ernesto-g/modular-synth/FINISHED/ATVMixer/Front Panel Blueprint/ATV_MIXER_front_panel.png

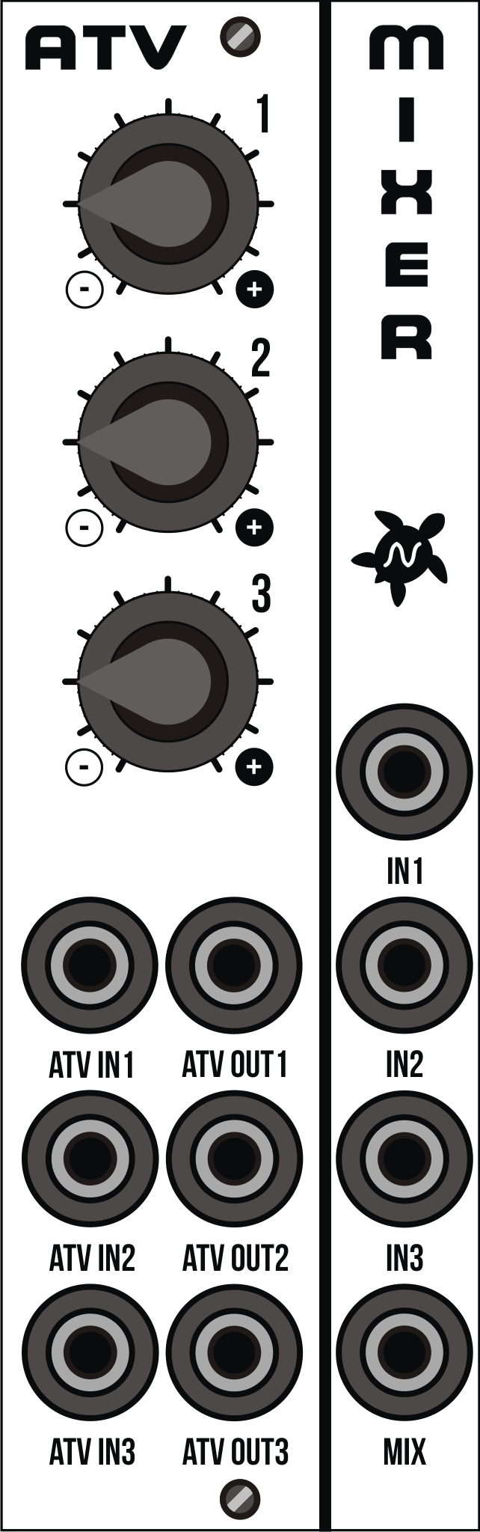
FINISHED/ATVMixer/Front Panel Blueprint/ATV_MIXER_front_panel.png
