ernesto-g/modular-synth/FINISHED/ATVMixer/PICTURES/1.jpg

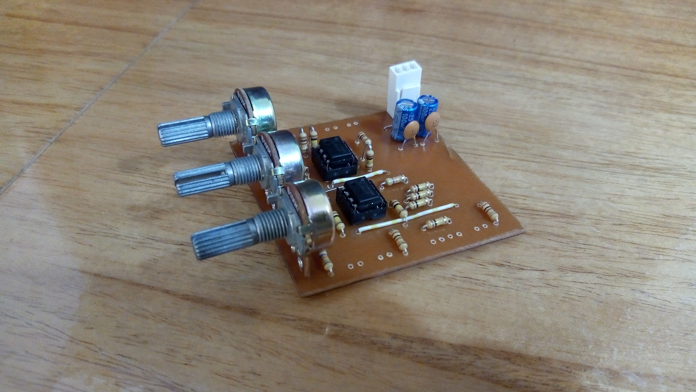
FINISHED/ATVMixer/PICTURES/1.jpg
