ernesto-g/modular-synth/FINISHED/ATVMixer/PICTURES/2.jpg

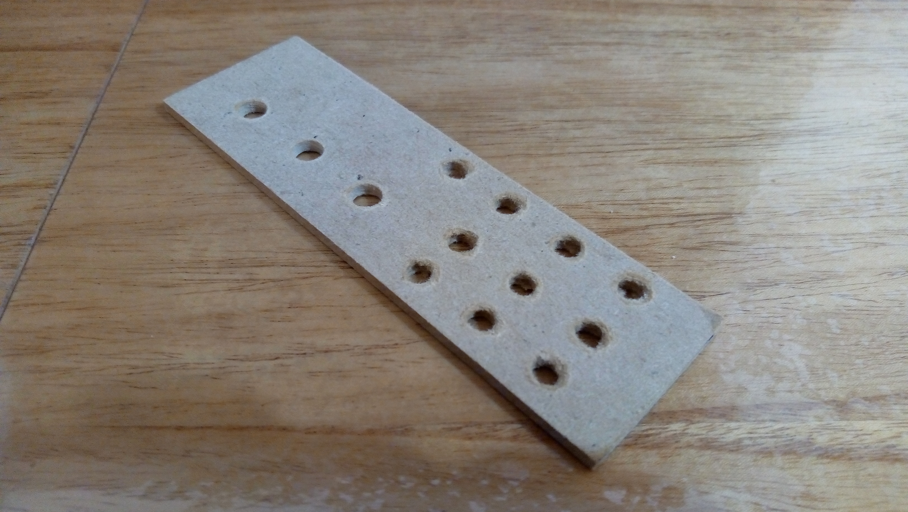
FINISHED/ATVMixer/PICTURES/2.jpg
