ernesto-g/modular-synth/FINISHED/IOS/Front Panel Blueprint/FRONT_PANEL_IOS.png

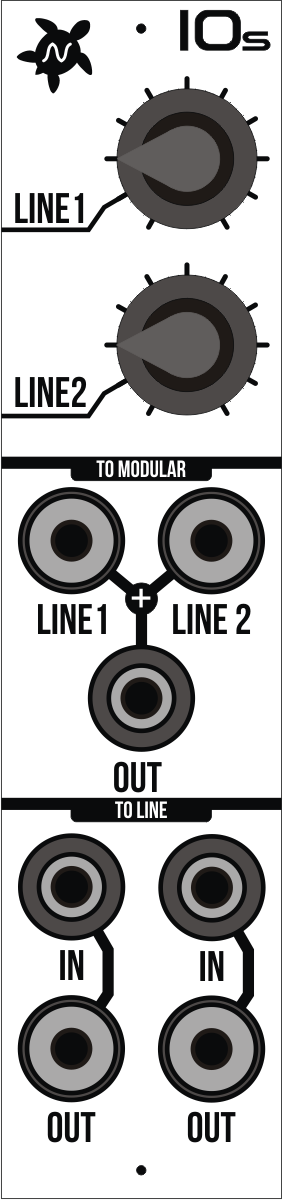
FINISHED/IOS/Front Panel Blueprint/FRONT_PANEL_IOS.png
