ernesto-g/modular-synth/FINISHED/IOS/IOSData/Line_levels.svg.png

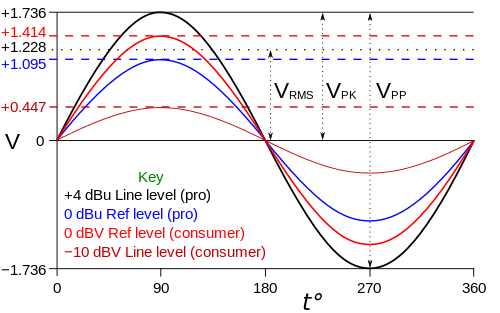
FINISHED/IOS/IOSData/Line_levels.svg.png
