ernesto-g/modular-synth/FINISHED/LFOx3/Front Panel Blueprint/LFO_X3_Front_Panel.png

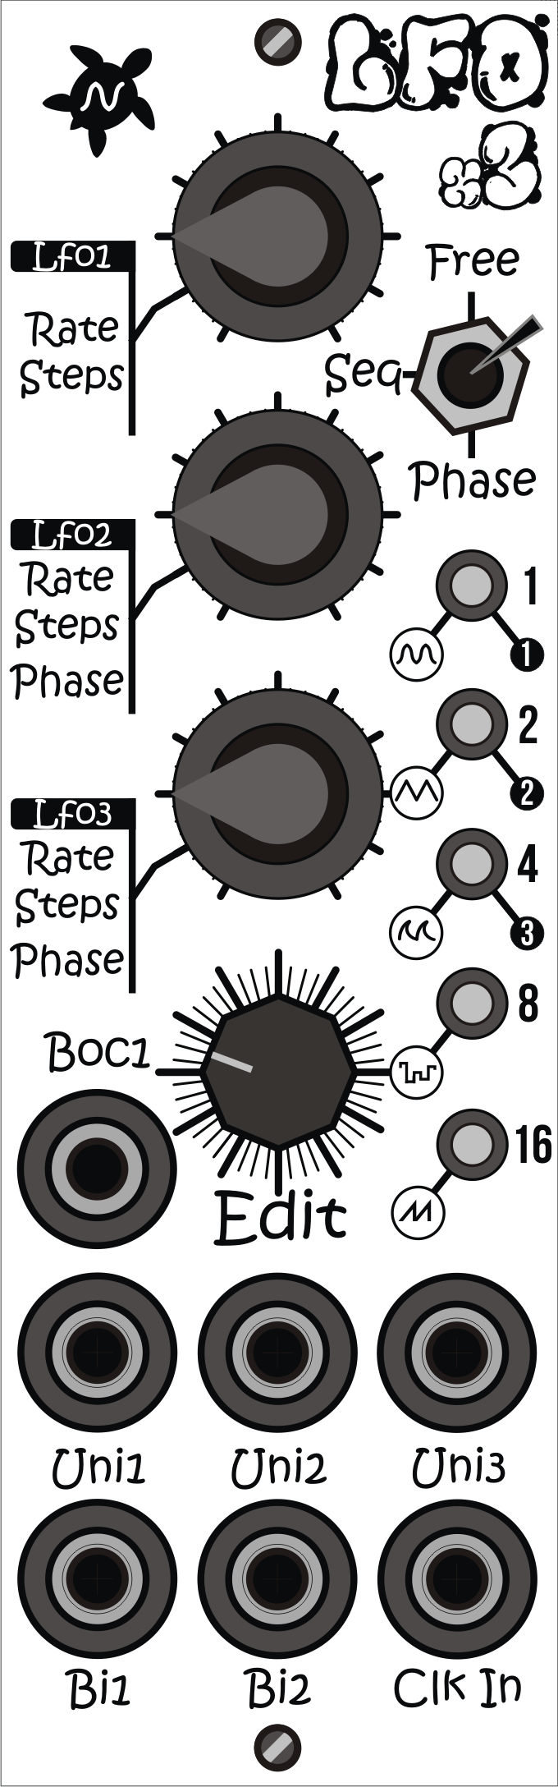
FINISHED/LFOx3/Front Panel Blueprint/LFO_X3_Front_Panel.png
