ernesto-g/modular-synth/FINISHED/SEQUENCER/Front Panel Blueprint/Font/A-Space_750.png

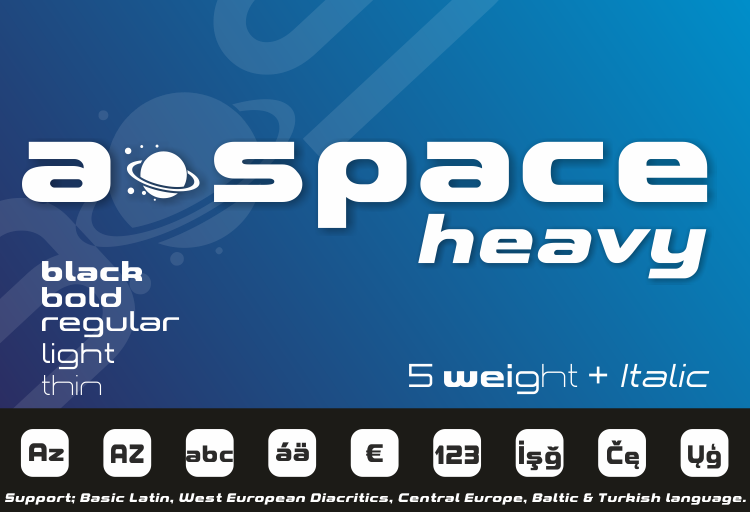
FINISHED/SEQUENCER/Front Panel Blueprint/Font/A-Space_750.png
