ernesto-g/modular-synth/FINISHED/SEQUENCER/Front Panel Blueprint/SEQ_FRONT_PANEL.png

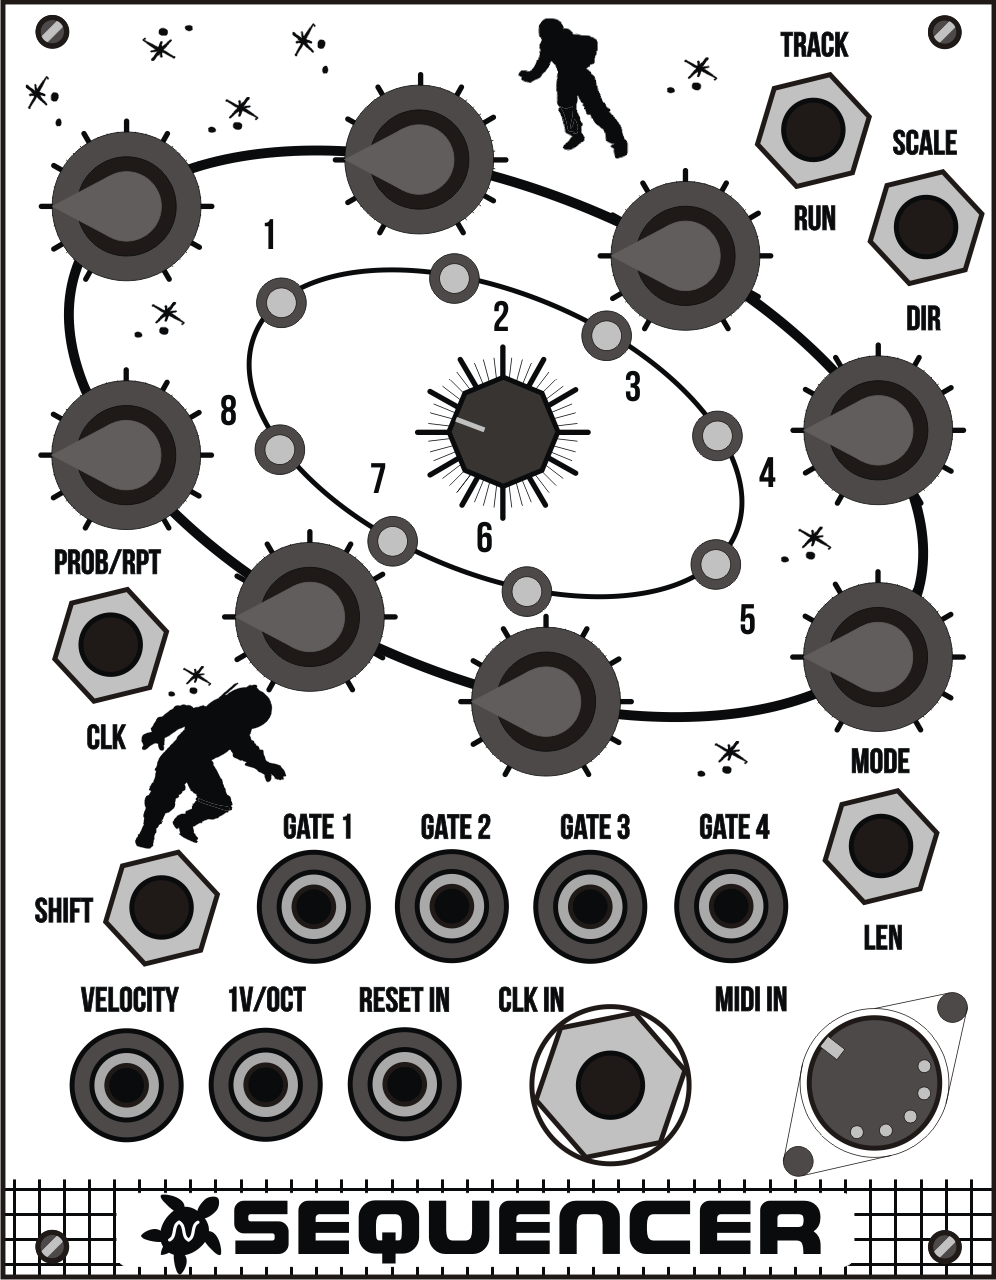
FINISHED/SEQUENCER/Front Panel Blueprint/SEQ_FRONT_PANEL.png
