ernesto-g/modular-synth/FINISHED/SIMPLE_SEQUENCER/Front Panel Blueprint/SIMPLE_SEQUENCER_Front_Panel.png

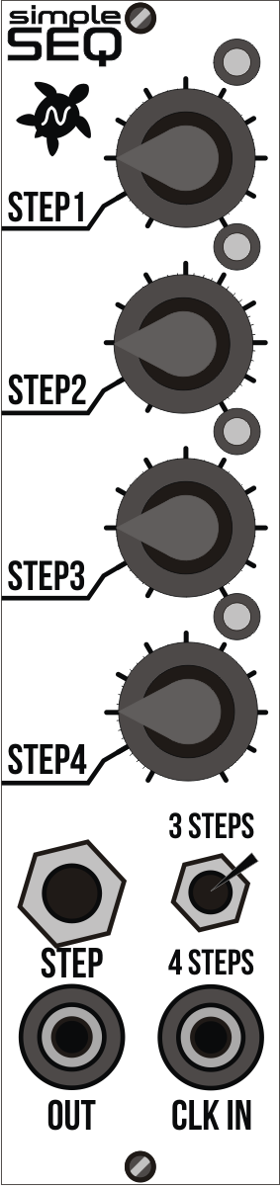
FINISHED/SIMPLE_SEQUENCER/Front Panel Blueprint/SIMPLE_SEQUENCER_Front_Panel.png
