ernesto-g/modular-synth/FINISHED/SIMPLE_SEQUENCER/PICTURES/1.jpg

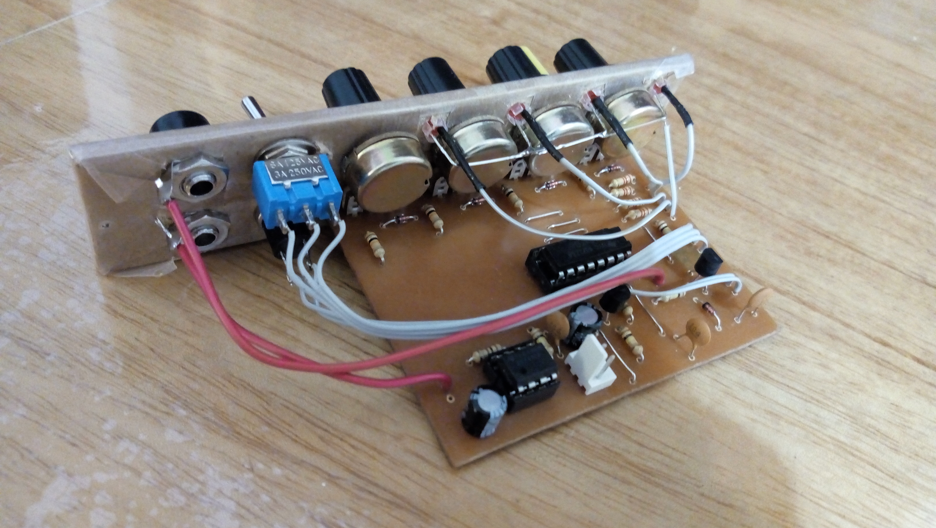
FINISHED/SIMPLE_SEQUENCER/PICTURES/1.jpg
