ernesto-g/modular-synth/FINISHED/SIMPLE_SEQUENCER/PICTURES/2.jpg

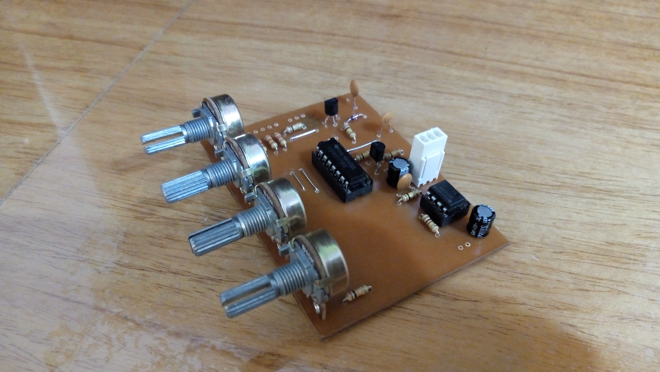
FINISHED/SIMPLE_SEQUENCER/PICTURES/2.jpg
