ernesto-g/modular-synth/FINISHED/SIMPLE_SEQUENCER/PICTURES/3.jpg

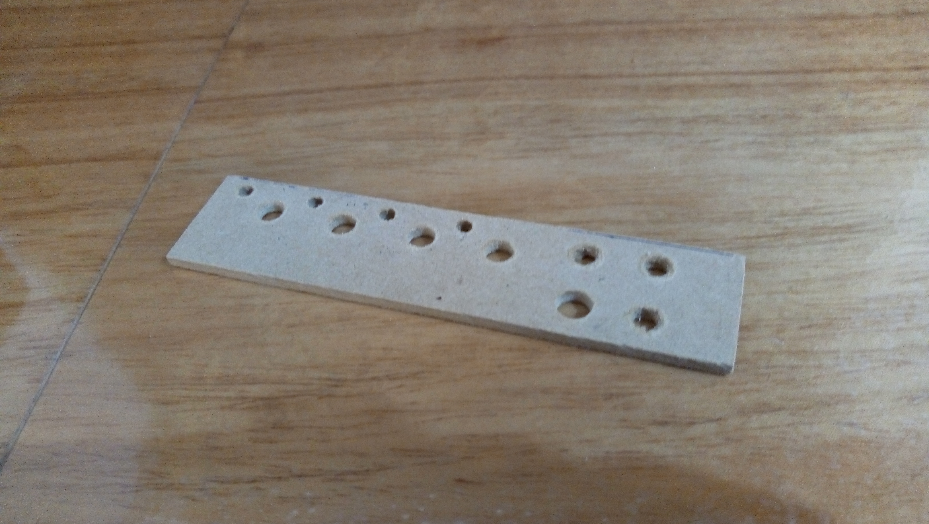
FINISHED/SIMPLE_SEQUENCER/PICTURES/3.jpg
