ernesto-g/modular-synth/FINISHED/SLEW_LIMITER/Front Panel Blueprint/FRONT_PANEL_SLEW_LIMITER.png

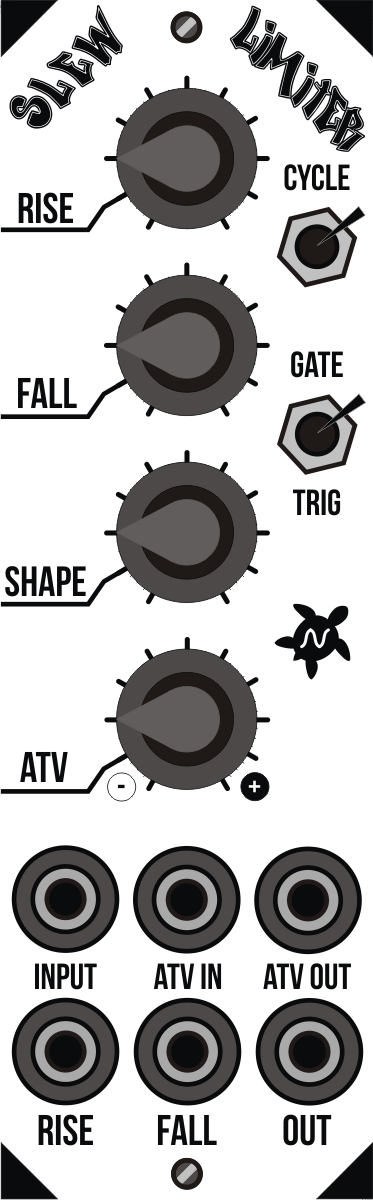
FINISHED/SLEW_LIMITER/Front Panel Blueprint/FRONT_PANEL_SLEW_LIMITER.png
