ernesto-g/modular-synth/FINISHED/SOUND_SOURCE/Front_Panel_blueprint/SOUND_SOURCE_FRONT_PANEL.png

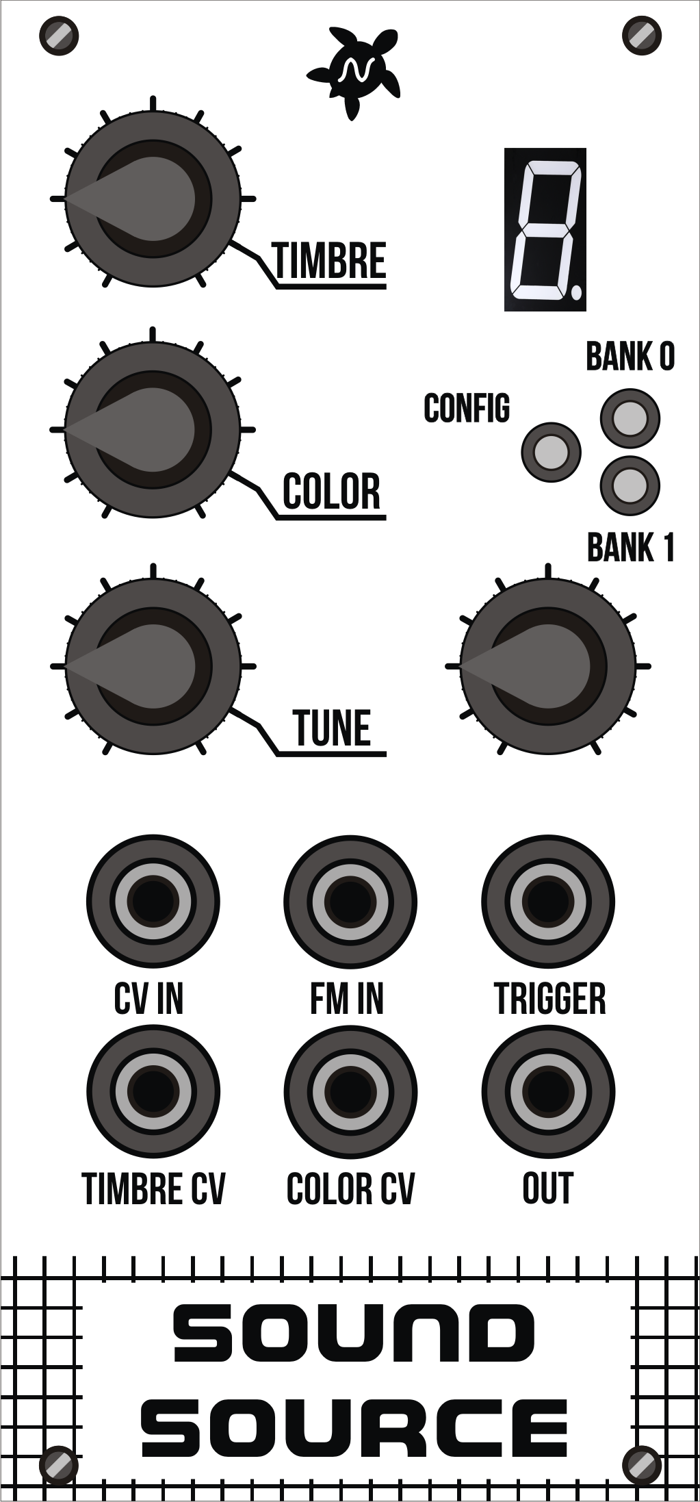
FINISHED/SOUND_SOURCE/Front_Panel_blueprint/SOUND_SOURCE_FRONT_PANEL.png
