ernesto-g/modular-synth/FINISHED/SOUND_SOURCE/Pictures/1.png

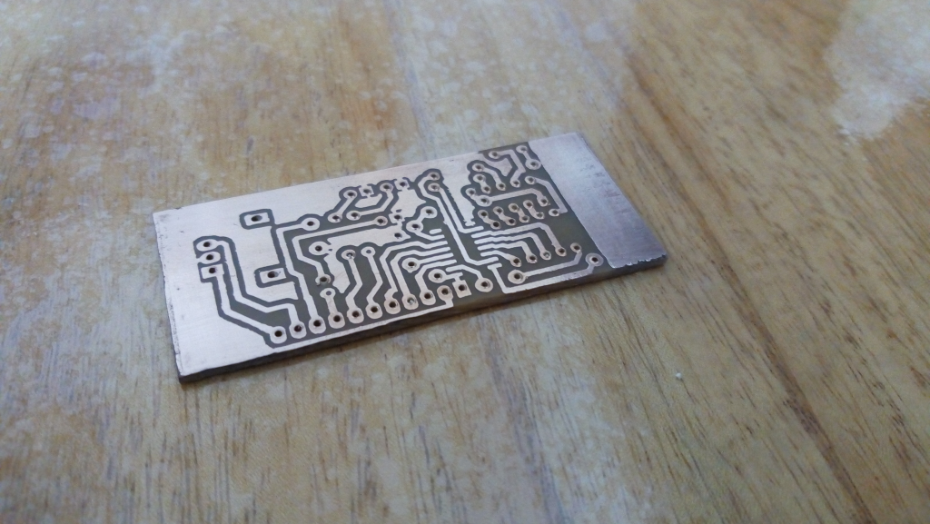
FINISHED/SOUND_SOURCE/Pictures/1.png
