ernesto-g/modular-synth/FINISHED/SOUND_SOURCE/Pictures/2.png

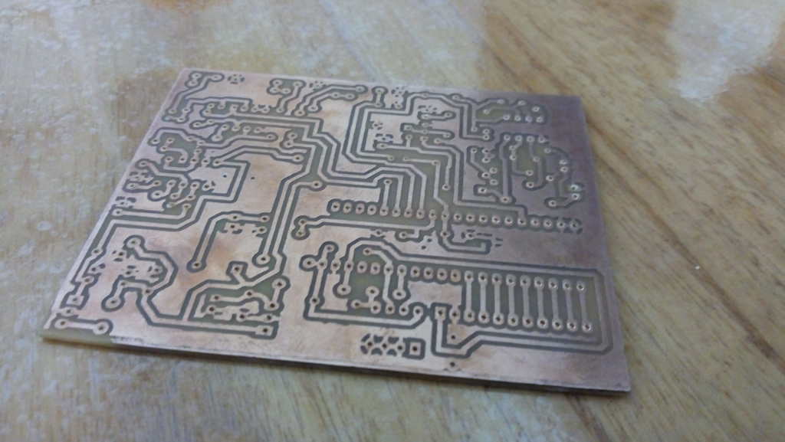
FINISHED/SOUND_SOURCE/Pictures/2.png
