ernesto-g/modular-synth/FINISHED/SOUND_SOURCE/Pictures/3.png

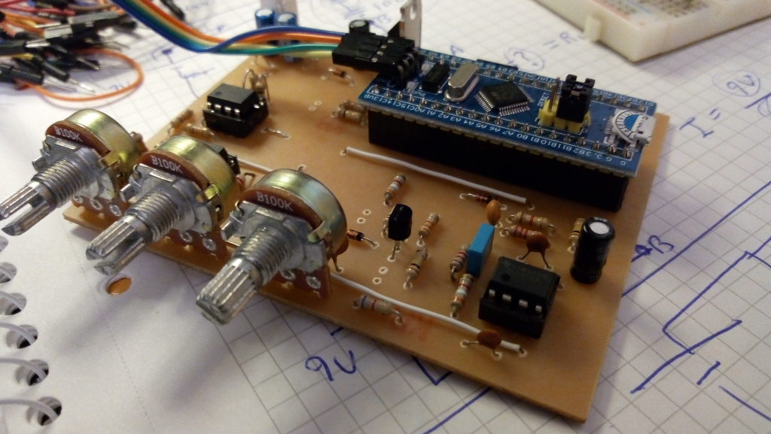
FINISHED/SOUND_SOURCE/Pictures/3.png
