ernesto-g/modular-synth/FINISHED/SOUND_SOURCE/Pictures/4.png

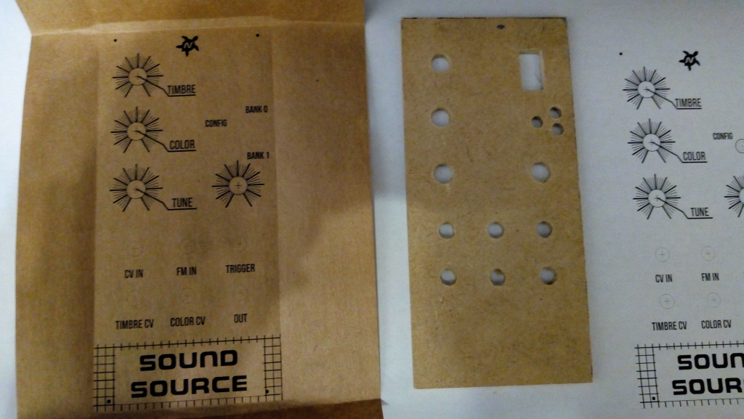
FINISHED/SOUND_SOURCE/Pictures/4.png
