ernesto-g/modular-synth/FINISHED/SOUND_SOURCE/Pictures/6.png

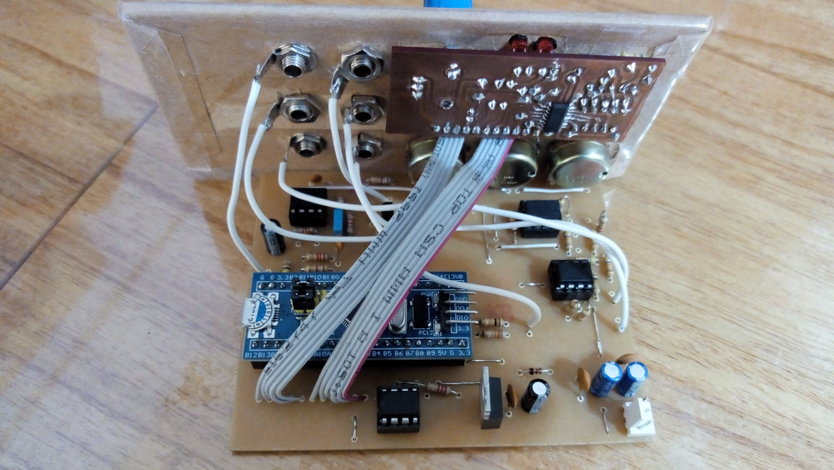
FINISHED/SOUND_SOURCE/Pictures/6.png
