ernesto-g/modular-synth/FINISHED/SOUND_SOURCE/Pictures/7.png

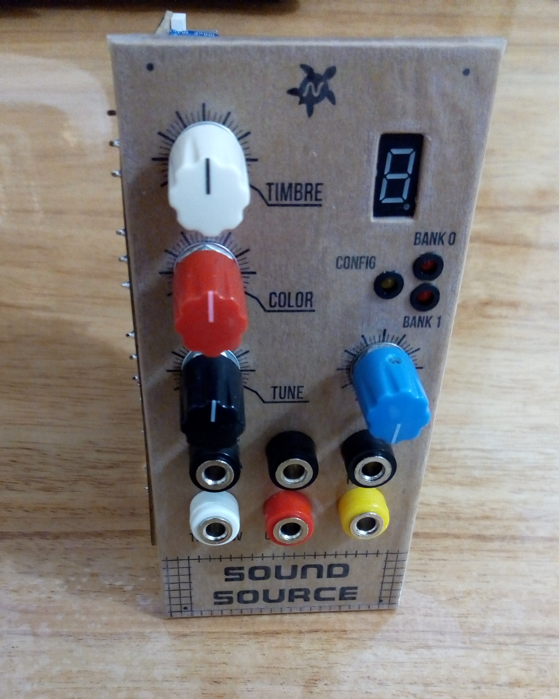
FINISHED/SOUND_SOURCE/Pictures/7.png
