ernesto-g/modular-synth/FINISHED/SOUND_SOURCE/Pictures/8.png

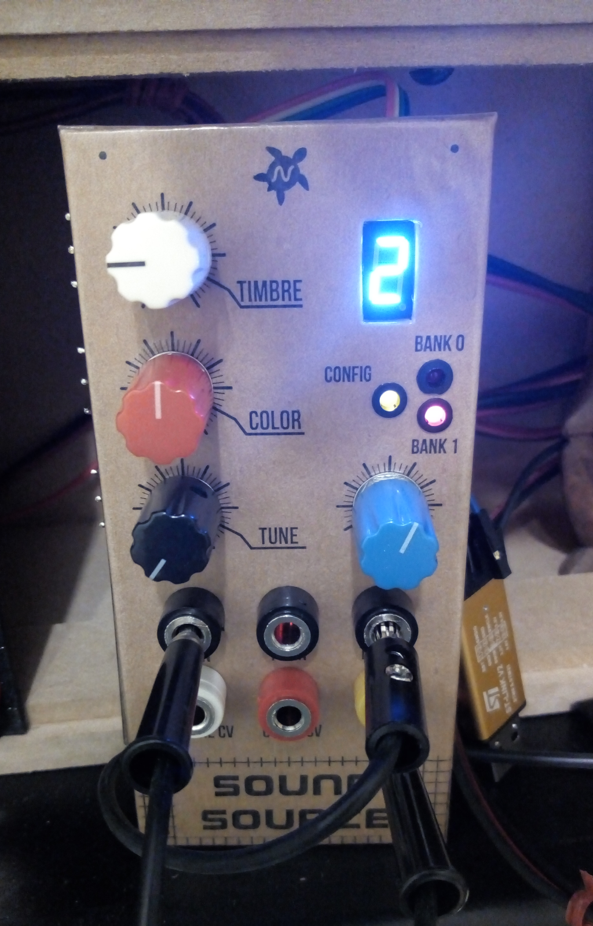
FINISHED/SOUND_SOURCE/Pictures/8.png
