ernesto-g/modular-synth/FINISHED/VCA/Front Panel Blueprint/VCA_FRONT_PANEL.png

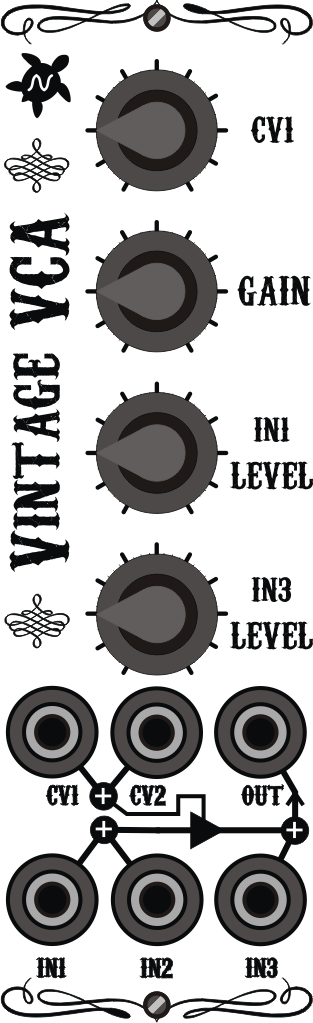
FINISHED/VCA/Front Panel Blueprint/VCA_FRONT_PANEL.png
