ernesto-g/modular-synth/FINISHED/VCO/Front panel blueprint/VCO_FRONT_PANEL.png

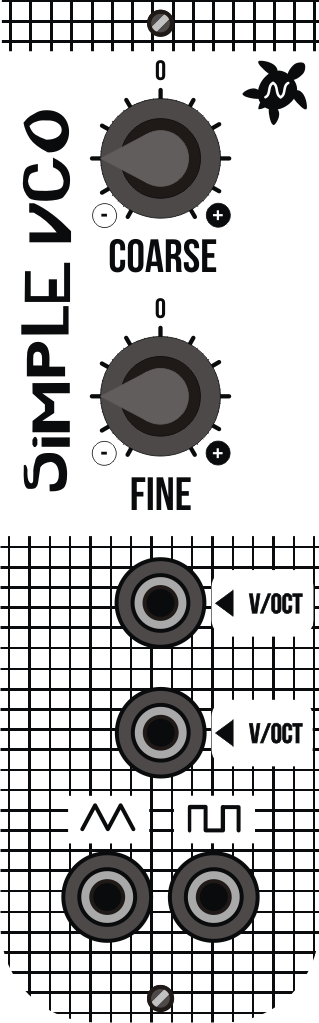
FINISHED/VCO/Front panel blueprint/VCO_FRONT_PANEL.png
