ernesto-g/modular-synth/UNFINISHED/INDUSTRIAL_KICK/signal_1.png

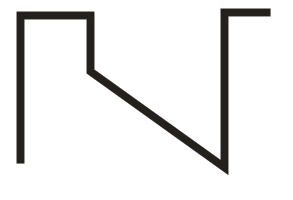
UNFINISHED/INDUSTRIAL_KICK/signal_1.png
