ernesto-g/modular-synth/UNFINISHED/INDUSTRIAL_KICK/signal_2.png

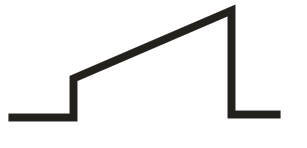
UNFINISHED/INDUSTRIAL_KICK/signal_2.png
