ernesto-g/modular-synth/UNFINISHED/INDUSTRIAL_KICK/signal_3.png

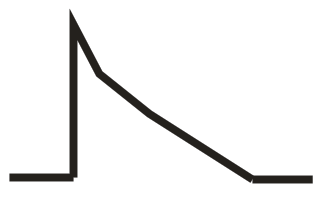
UNFINISHED/INDUSTRIAL_KICK/signal_3.png
