ernesto-g/modular-synth/UNFINISHED/INDUSTRIAL_KICK/signal_4.png

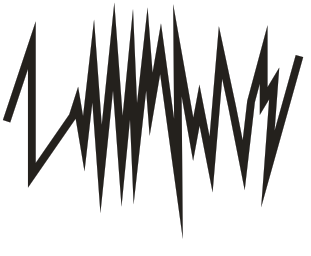
UNFINISHED/INDUSTRIAL_KICK/signal_4.png
