ernesto-g/modular-synth/FINISHED/SIMPLE_SEQUENCER/SIMPLE_SEQUENCER_modular_PCB/DIY/SIMPLE_SEQUENCER_wires_and_connectors.pdf

# Rear View

J2_1

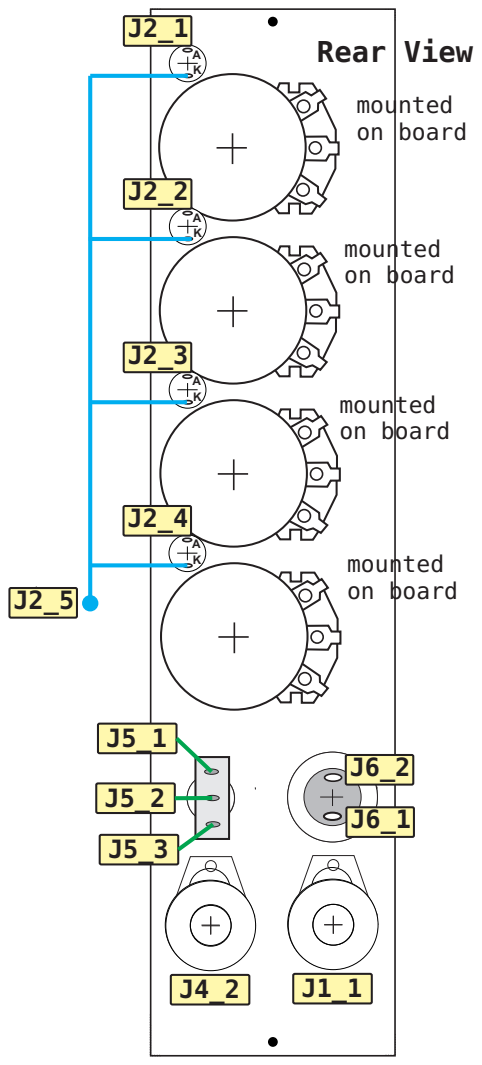
[picture p37: page 1]
mounted; on board
