ernesto-g/modular-synth/FINISHED/ATVMixer/ATV_AND_MIXER_modular_PCB/DIY/ATV_MIXER_FRONT_PANEL_HOLES.pdf

7mm

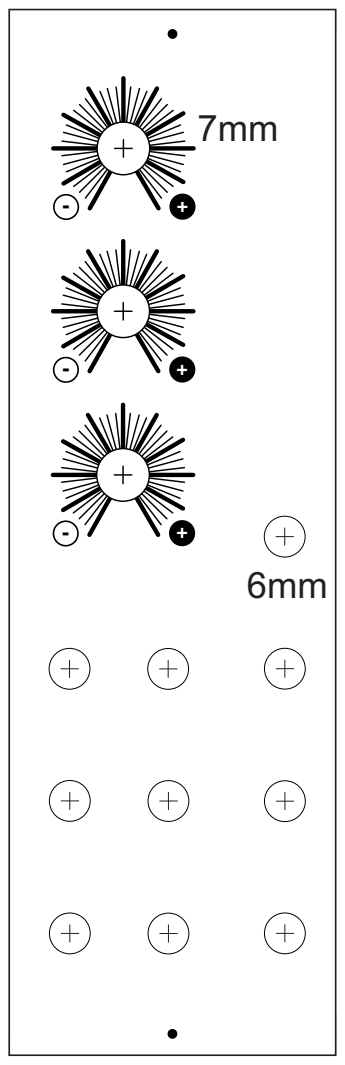
[picture p38: page 1]
