ernesto-g/modular-synth/FINISHED/ATVMixer/ATV_AND_MIXER_modular_PCB/DIY/ATV_MIXER_FRONT_PANEL_wires_and_connectors.pdf

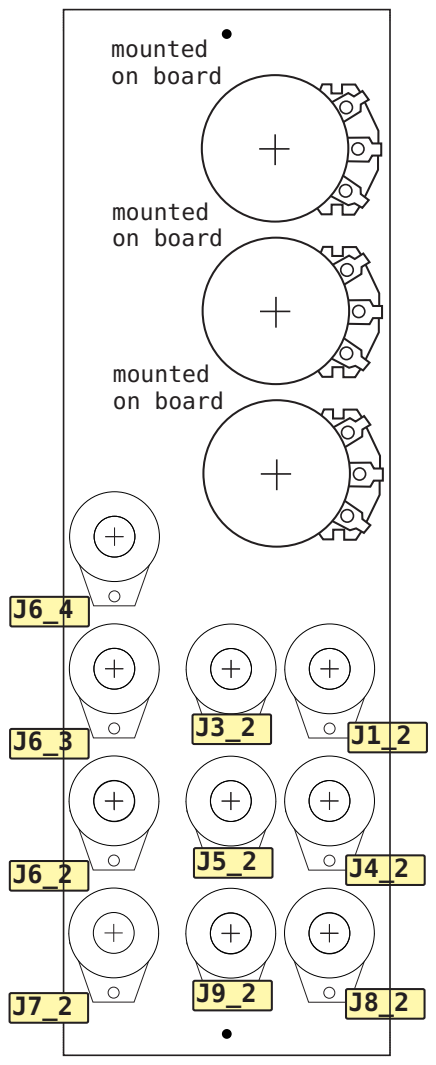
[picture p39: page 1]
mounted; on board
