ernesto-g/modular-synth/FINISHED/LFOx3/LFO_modular_PCB/DIY/LFO_X3_FRONT_PANEL_wires_and_connectors.pdf

J7_1

J7_2

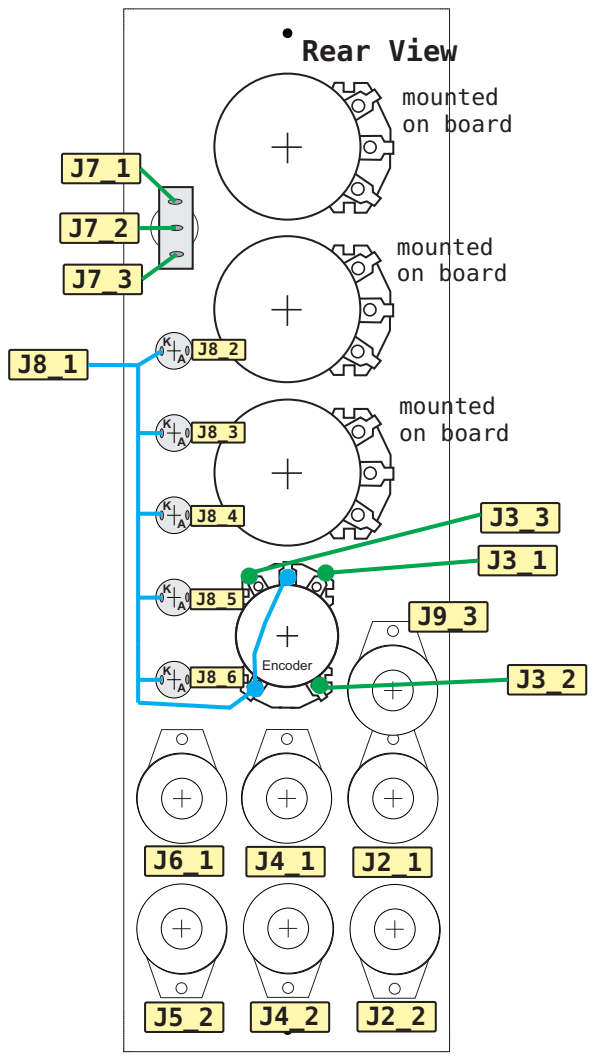
[picture p40: page 1]
mounted; on board; Rear View; Encoder
