ernesto-g/modular-synth/FINISHED/SOUND_SOURCE/SOUND_SOURCE_modular_PCB/DIY/SOUND_SOURCE_FRONT_PANEL_wires_and_connectors.pdf

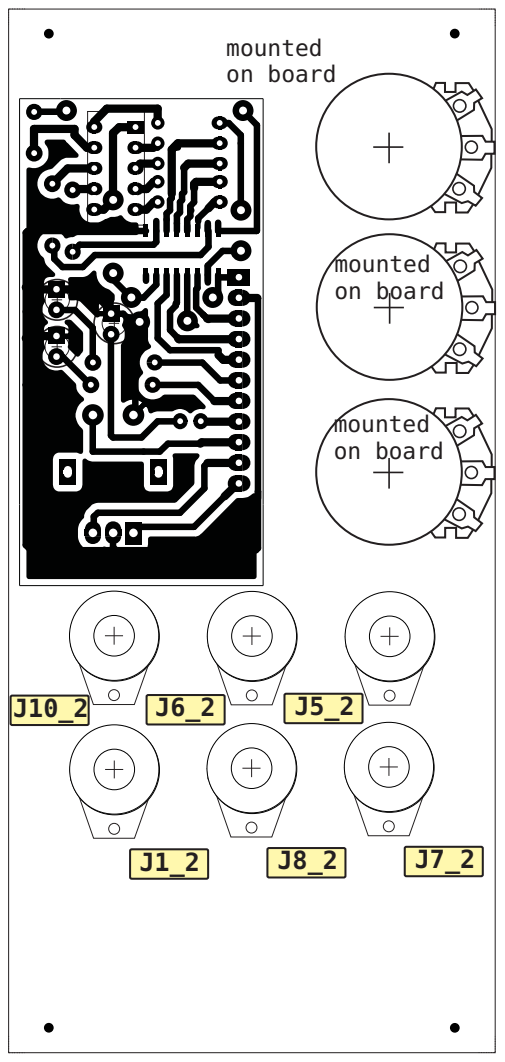
[picture p41: page 1]
mounted; on board
