ernesto-g/modular-synth/FINISHED/IOS/IOS_modular_PCB/DIY/IOS_FRONT_PANEL_wires_and_connectors.pdf

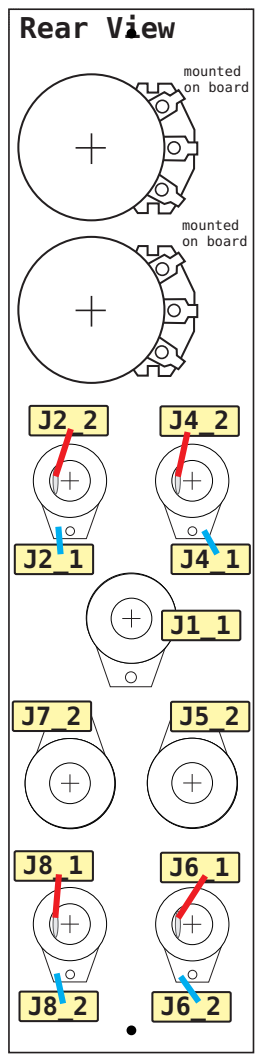
[picture p42: page 1]
mounted; on board; Rear View
