ernesto-g/modular-synth/FINISHED/SEQUENCER/SEQUENCER_modular_PCB/DIY/SEQ_FRONT_PANEL.pdf

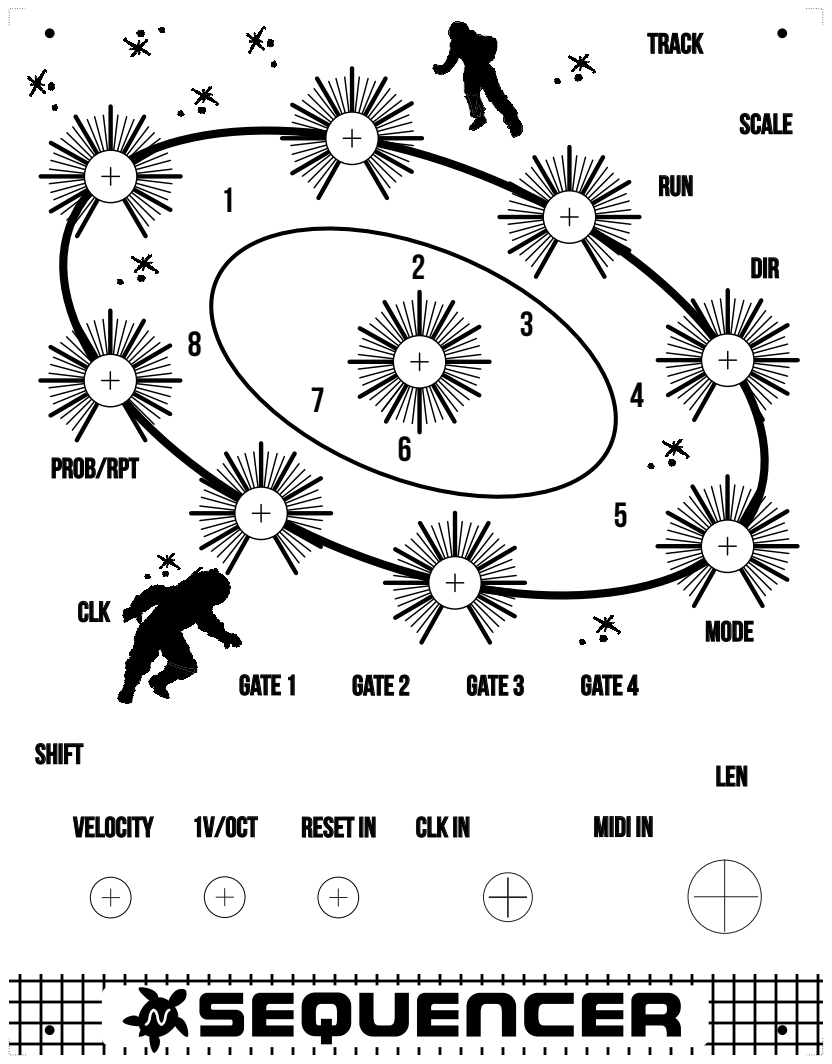
[picture p43: page 1]
VELOCITY; 1V/oct; RESET IN; CLK IN; TRACK; RUN; MODE; LEN; CLK; PROB/RPT; SHIFT; SCALE; DIR; MIDI IN; Gate 1; Gate 2; Gate 3; Gate 4; SEQUENCER
