ernesto-g/modular-synth/FINISHED/SEQUENCER/SEQUENCER_modular_PCB/DIY/SEQ_FRONT_PANEL_wires_and_connectors.pdf

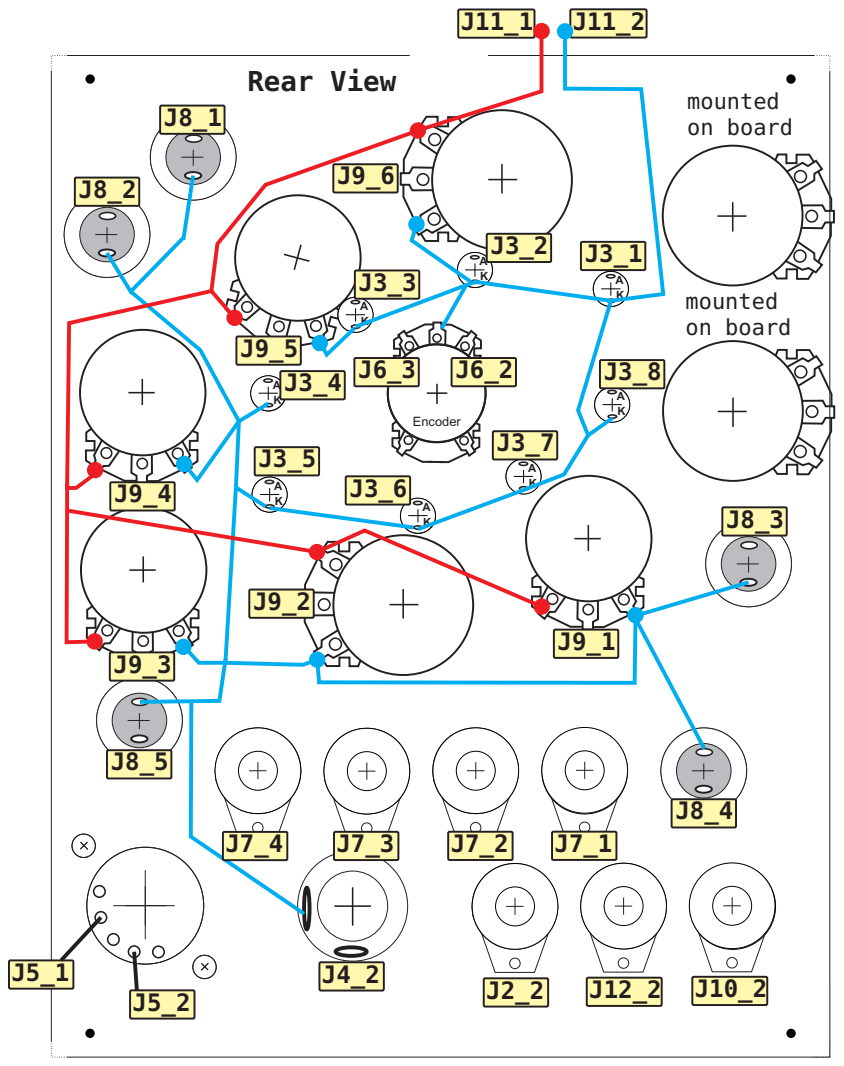
[picture p44: page 1]
Rear View; mounted; on board; Encoder
