ernesto-g/modular-synth/FINISHED/SLEW_LIMITER/SLEW_LIMITER_modular_PCB/DIY/SLEW_LIMITER_FRONT_PANEL_wires_and_connectors.pdf

# Rear View

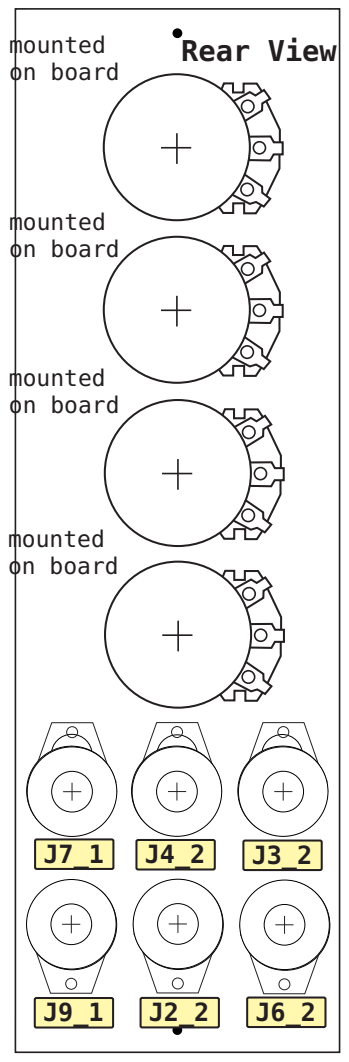
[picture p45: page 1]
mounted; on board
