ernesto-g/modular-synth/FINISHED/VCA/VCA_modular_PCB/DIY/VCA_FRONT_PANEL_wires_and_connectors.pdf

# Rear View

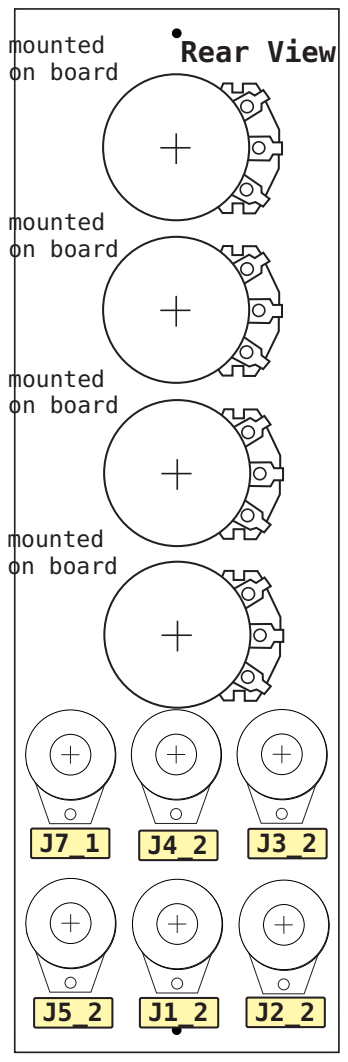
[picture p46: page 1]
mounted; on board
