ernesto-g/modular-synth/FINISHED/VCO/VCO_Modular_PCB/DIY/VCO_FRONT_PANEL_wires_and_connectors.pdf

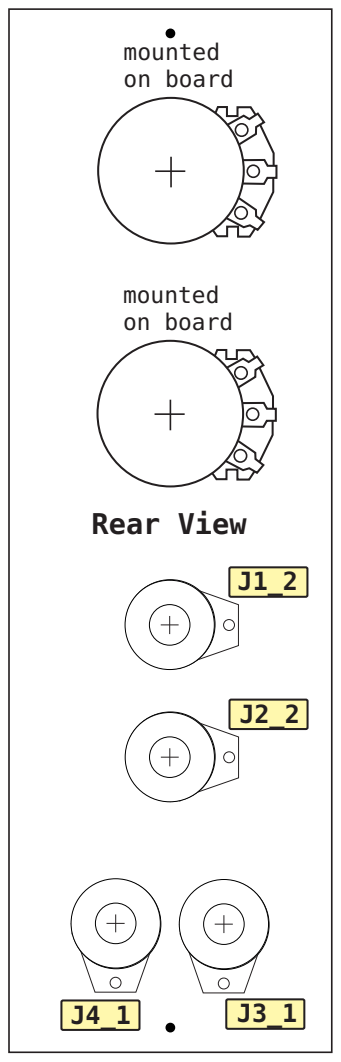
[picture p47: page 1]
Rear View; mounted; on board
