ernesto-g/modular-synth/FINISHED/SOUND_SOURCE/SOUND_SOURCE_modular_PCB/DIY/PCB_components.pdf

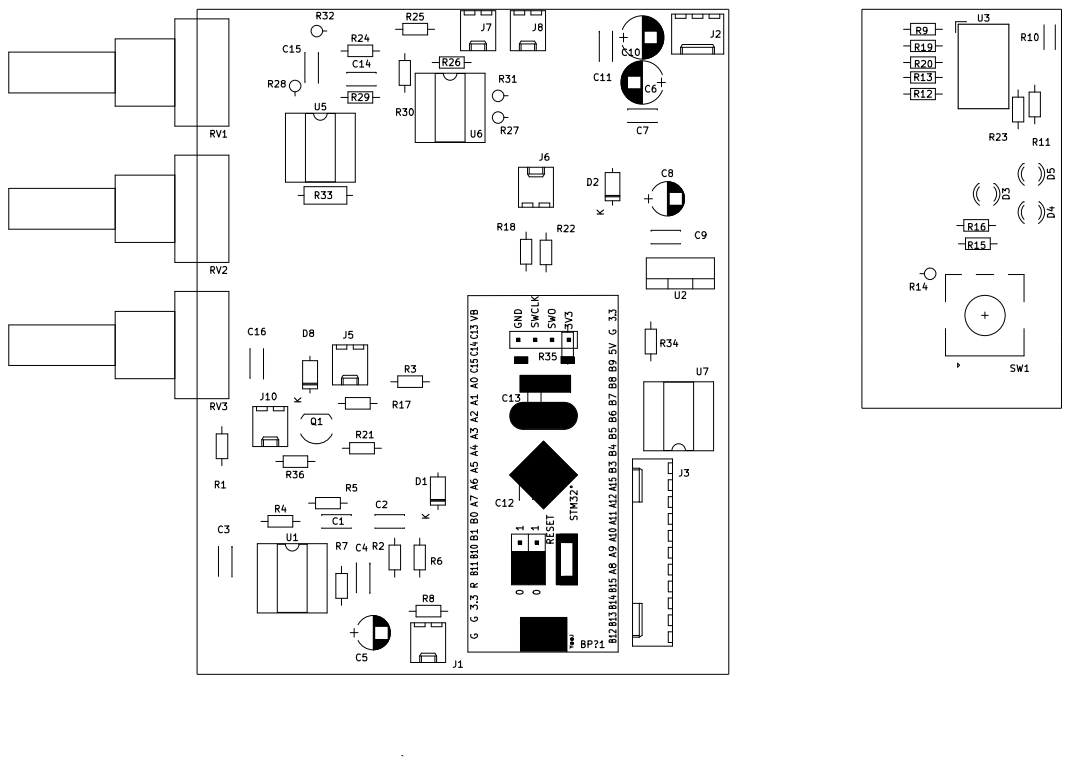
[picture p57: page 1]
