ernesto-g/modular-synth/FINISHED/IOS/IOS_modular_PCB/DIY/PCB_components.pdf

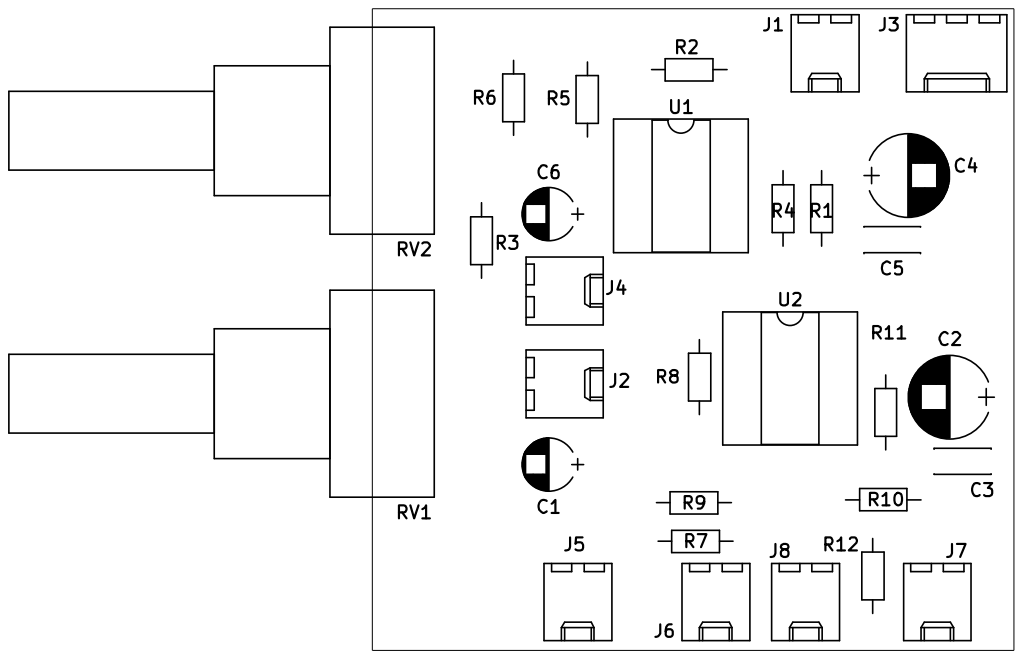
[picture p58: page 1]
