ernesto-g/modular-synth/FINISHED/IOS/IOS_modular_PCB/DIY/Schematic.pdf

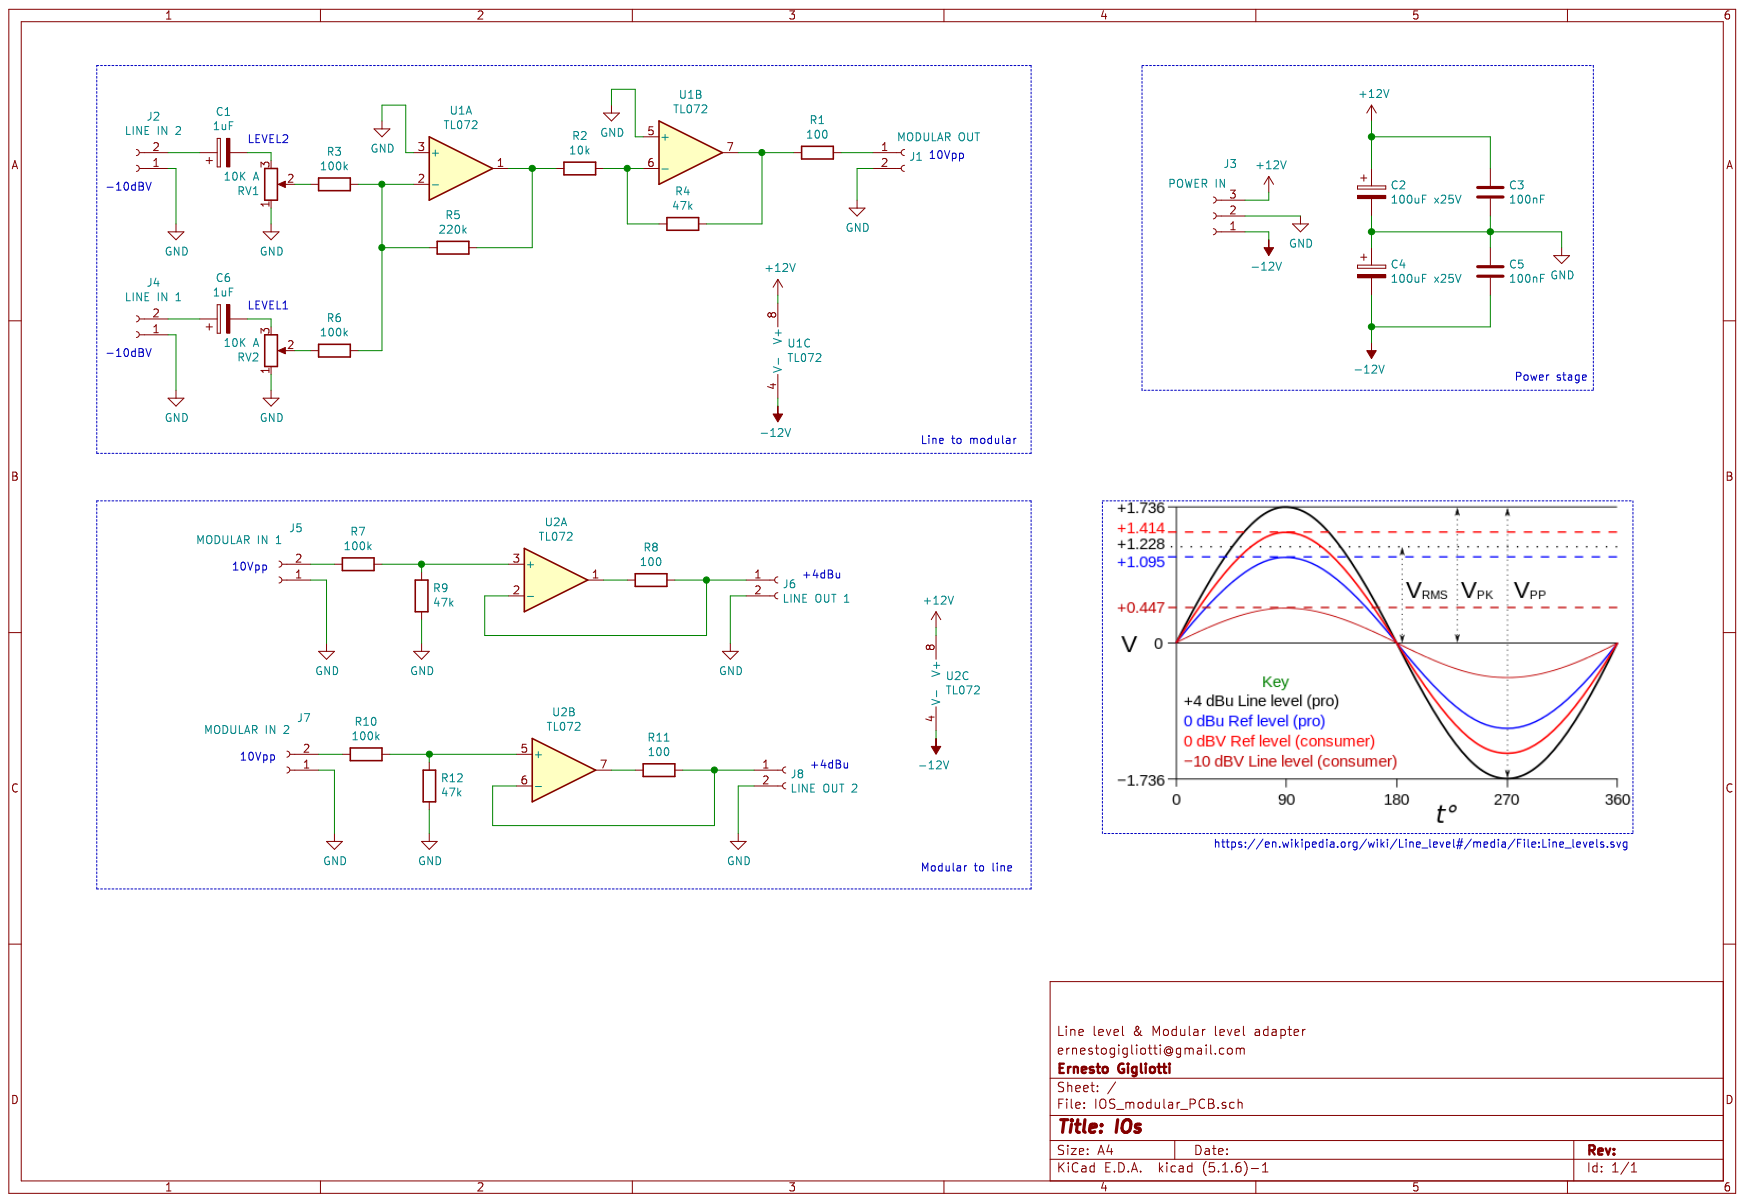
[picture p59: page 1]
