ernesto-g/modular-synth/FINISHED/SEQUENCER/SEQUENCER_modular_PCB/DIY/PCB_components.pdf

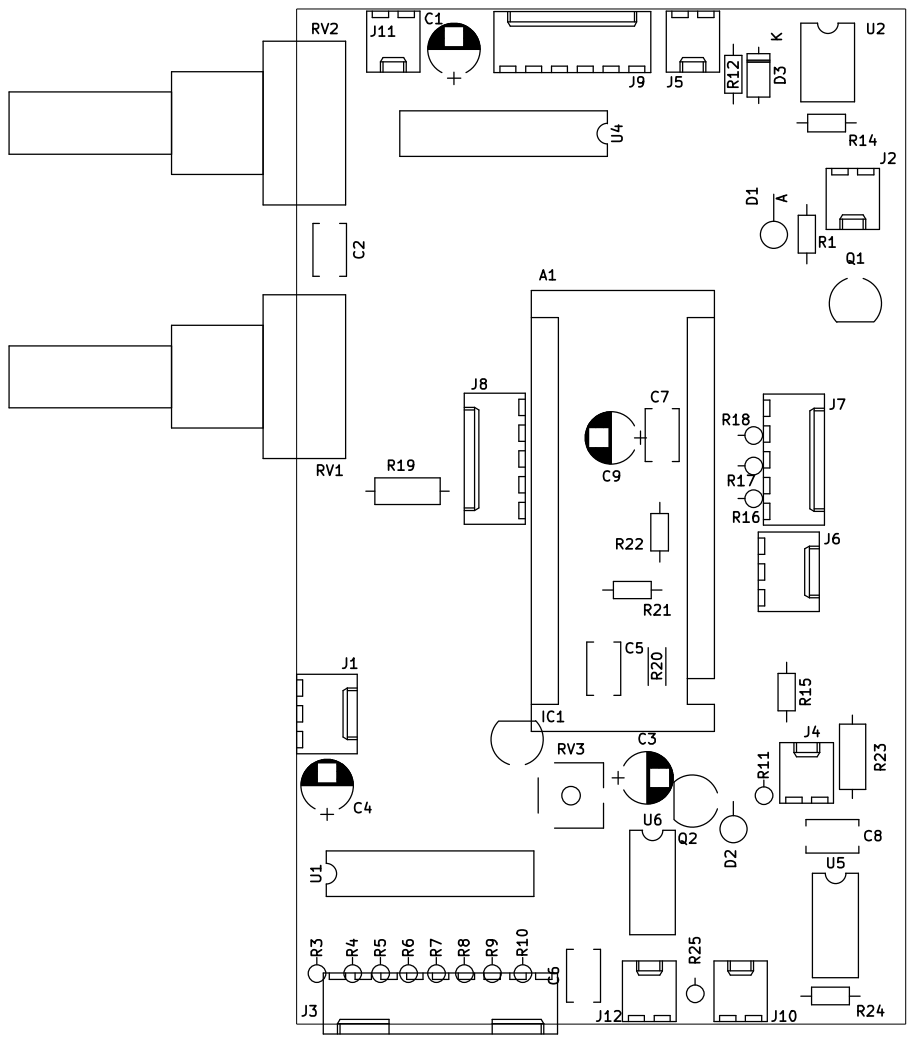
[picture p60: page 1]
