ernesto-g/modular-synth/FINISHED/SEQUENCER/SEQUENCER_modular_PCB/DIY/Schematic.pdf

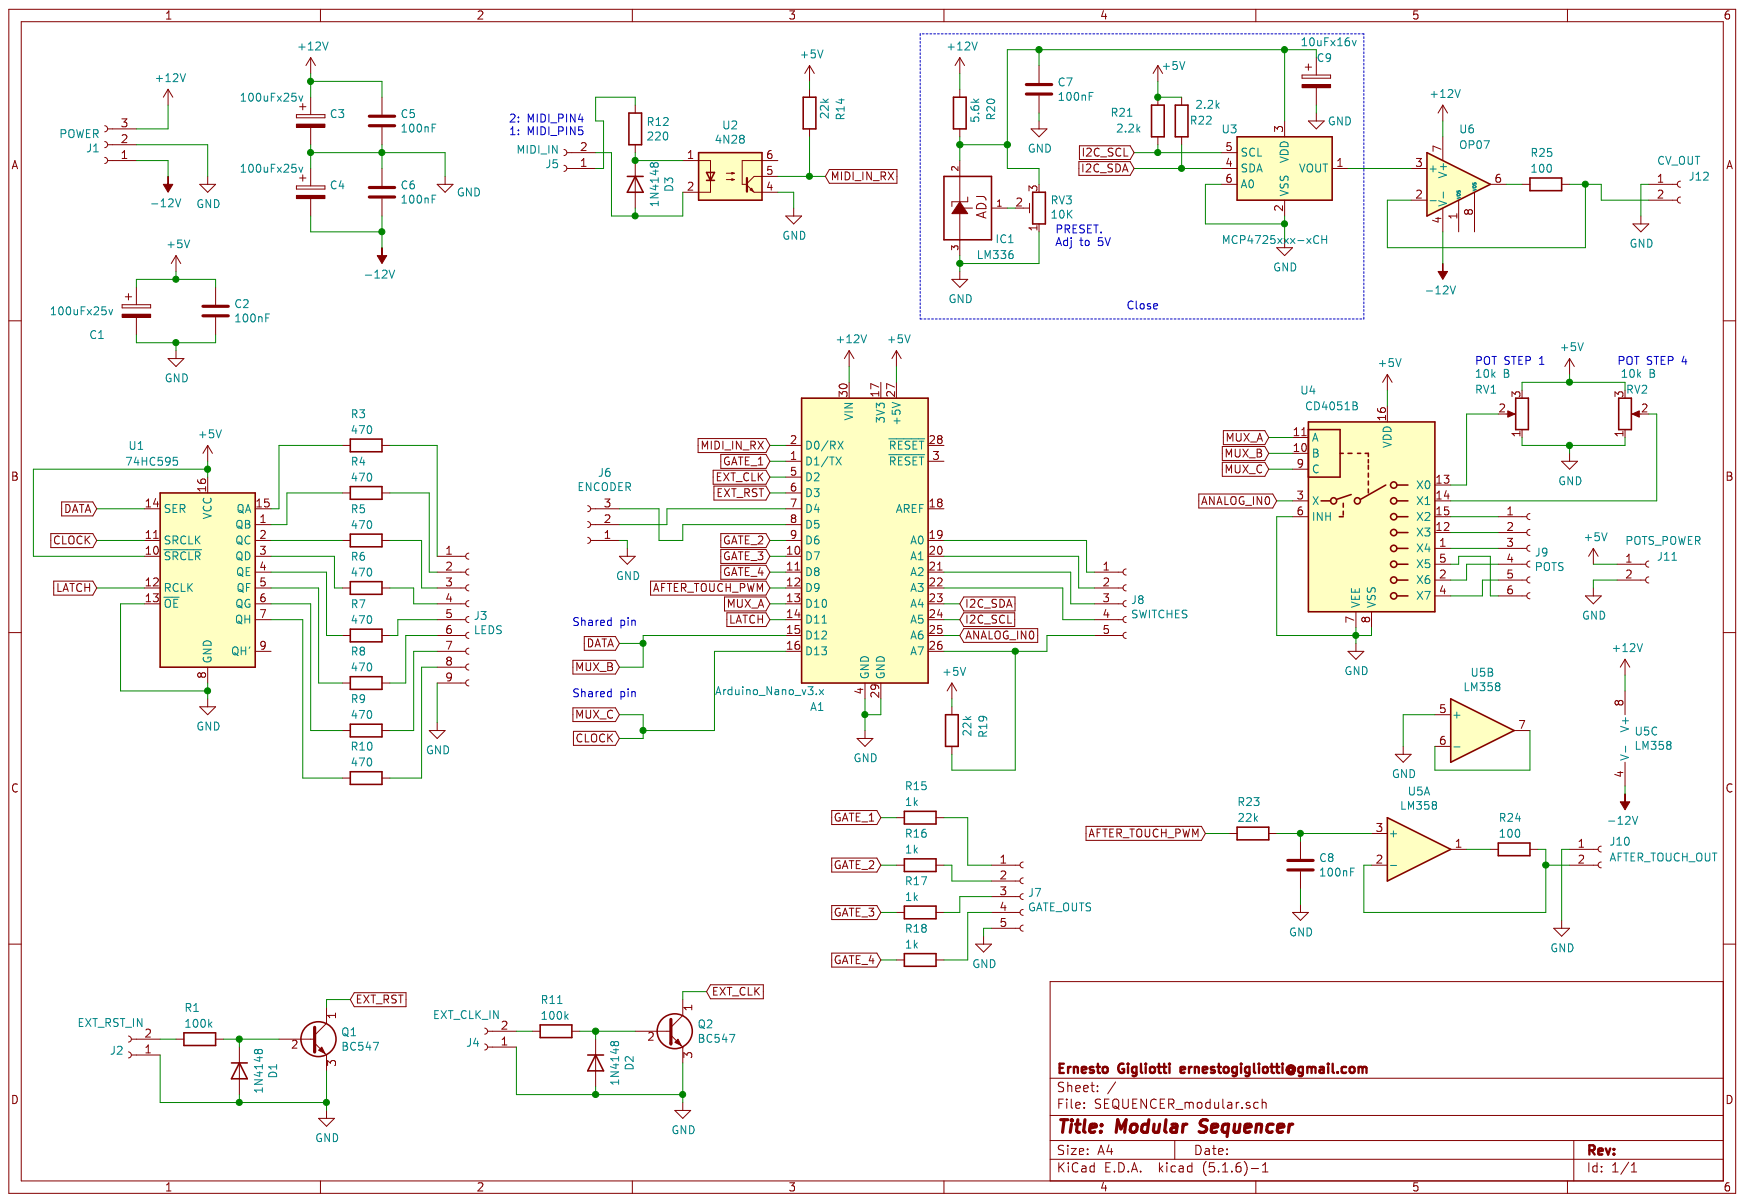
[picture p61: page 1]
