ernesto-g/modular-synth/FINISHED/SLEW_LIMITER/SLEW_LIMITER_modular_PCB/DIY/PCB_components.pdf

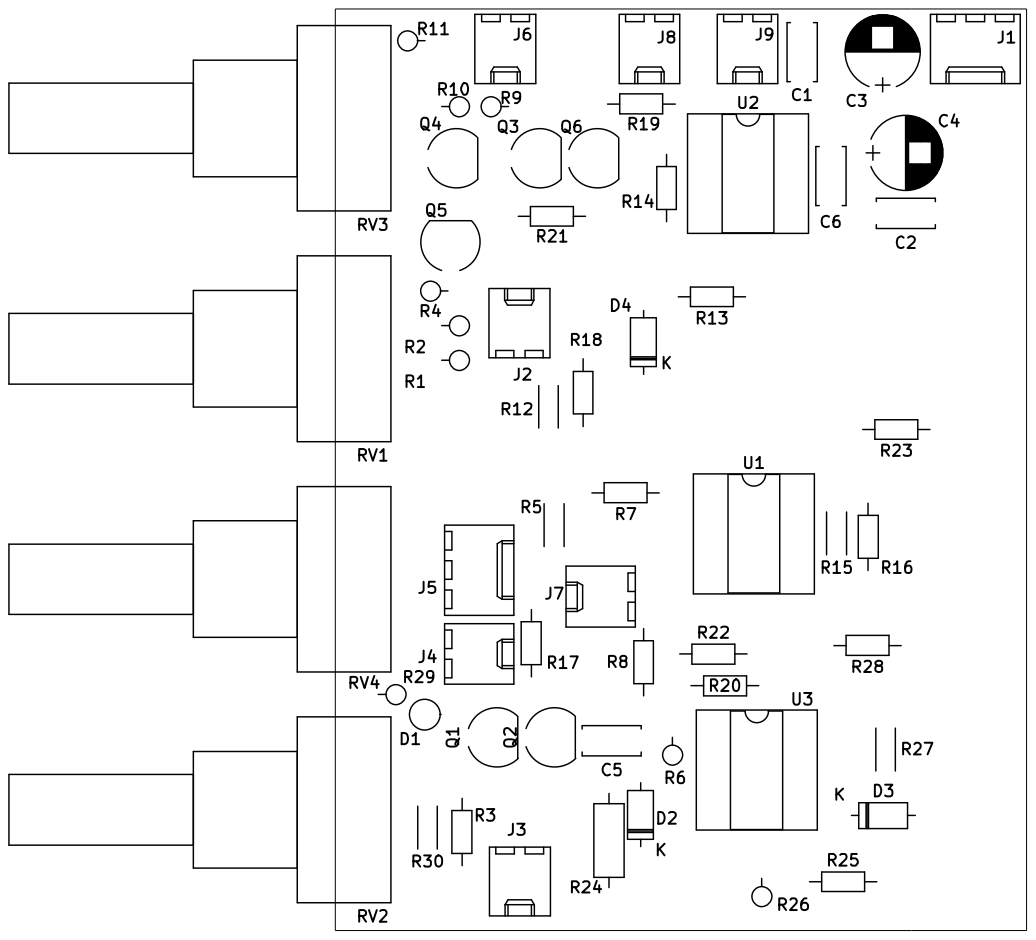
[picture p62: page 1]
