ernesto-g/modular-synth/FINISHED/SLEW_LIMITER/SLEW_LIMITER_modular_PCB/DIY/Schematic.pdf

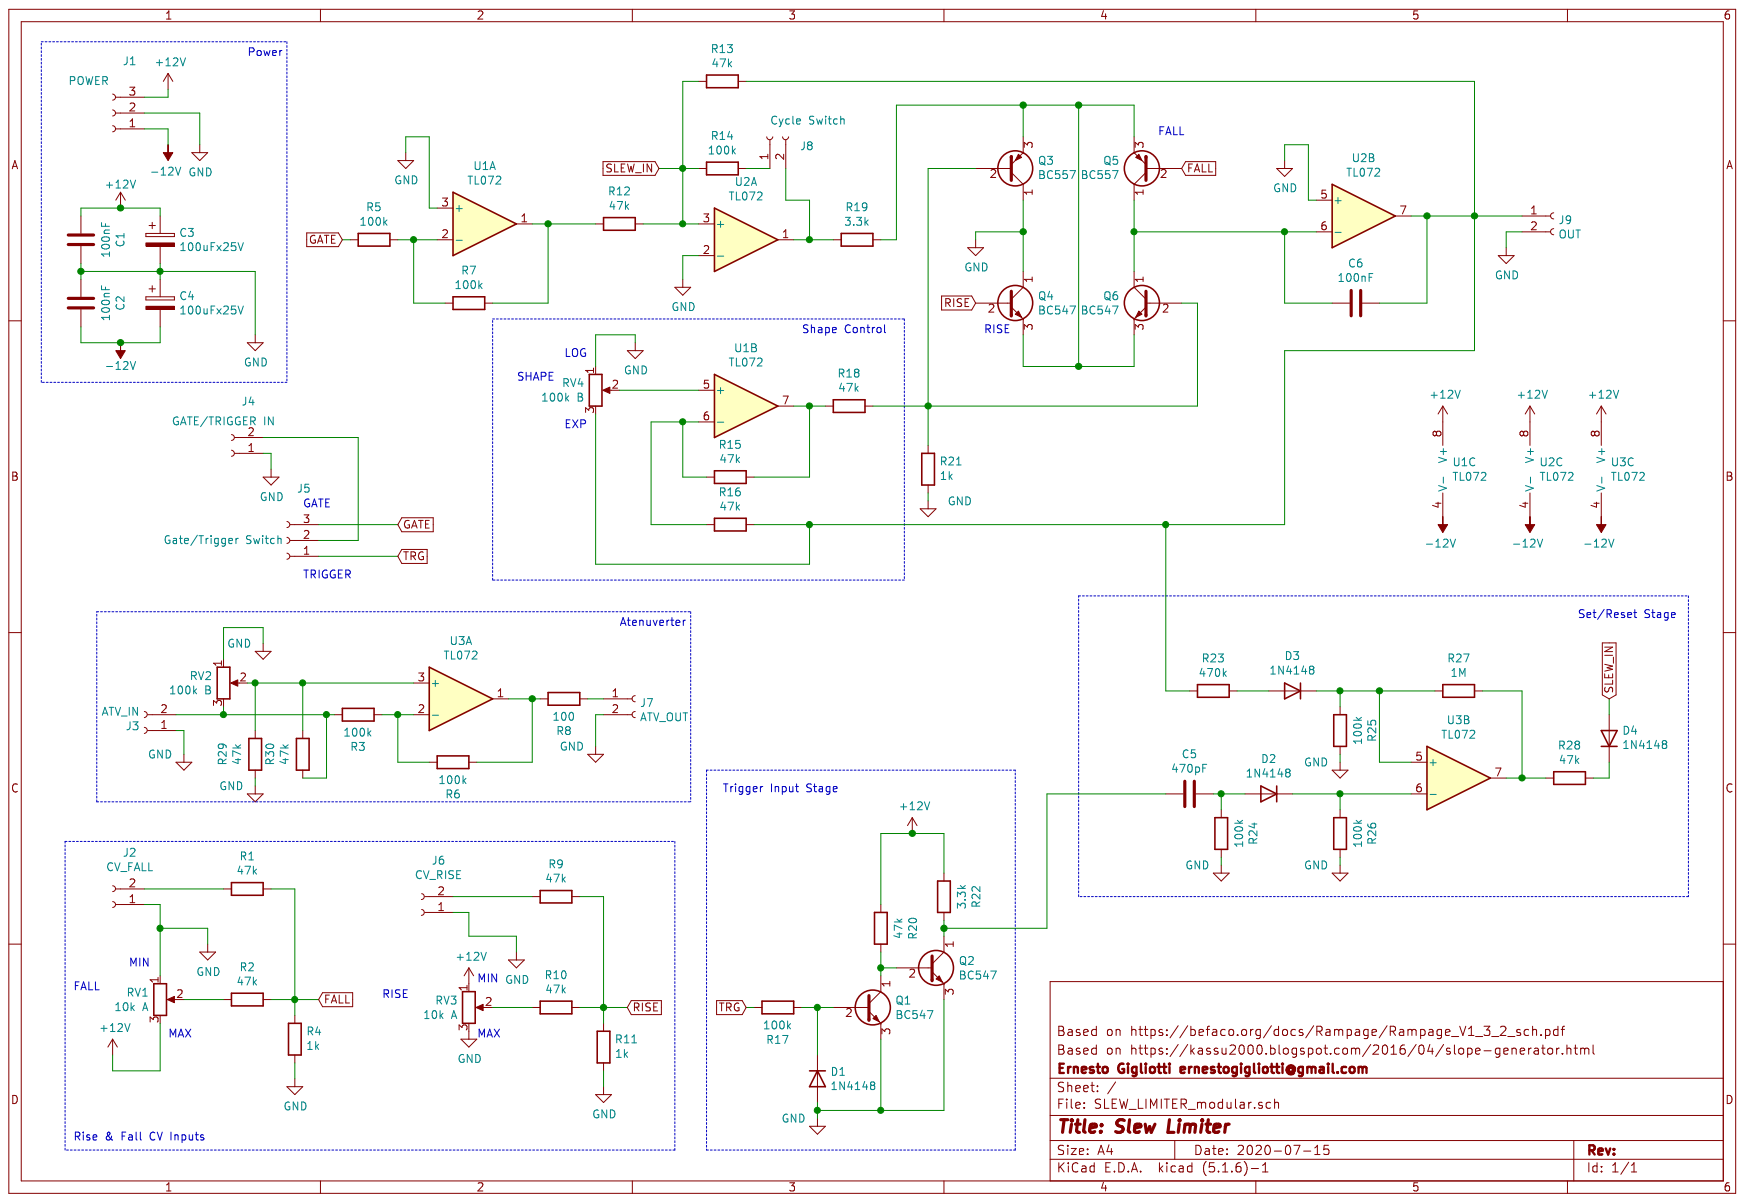
[picture p63: page 1]
