ernesto-g/modular-synth/FINISHED/VCA/VCA_modular_PCB/DIY/PCB_components.pdf

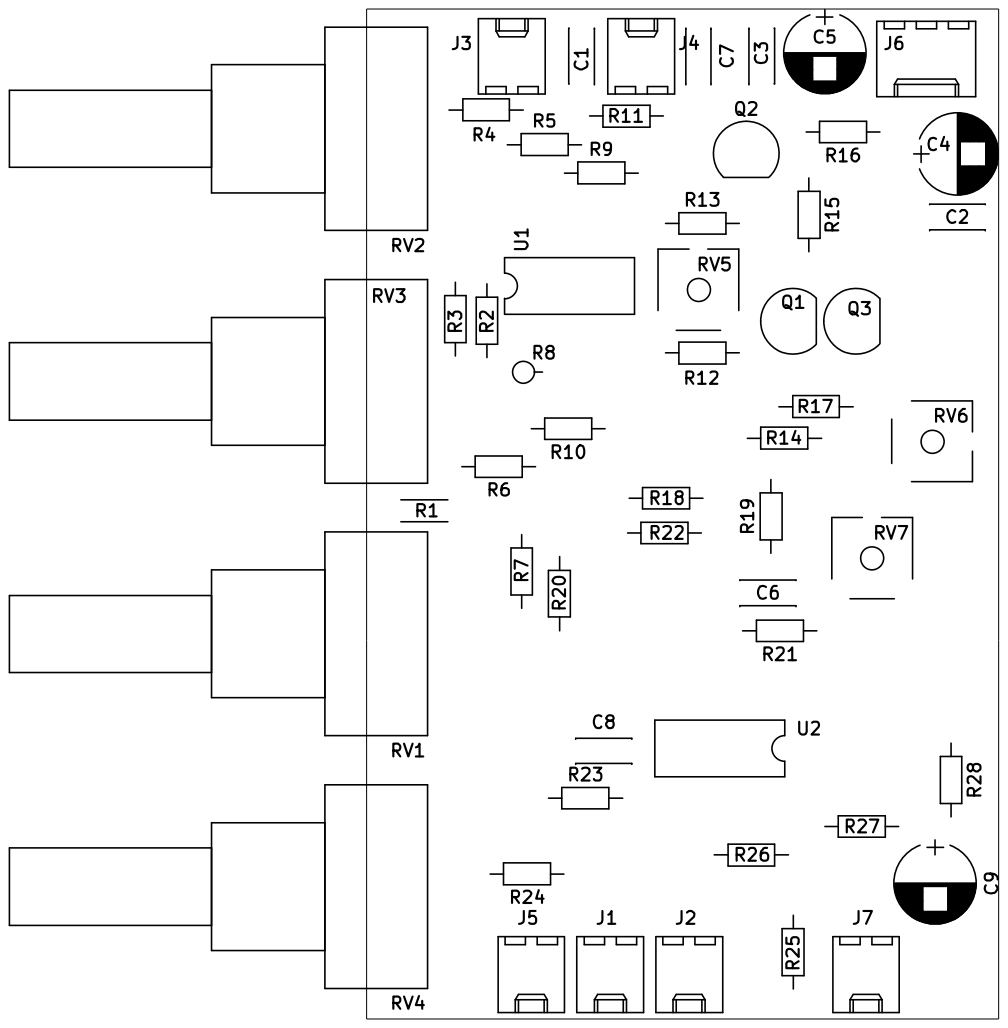
[picture p64: page 1]
