ernesto-g/modular-synth/FINISHED/VCA/VCA_modular_PCB/DIY/Schematic.pdf

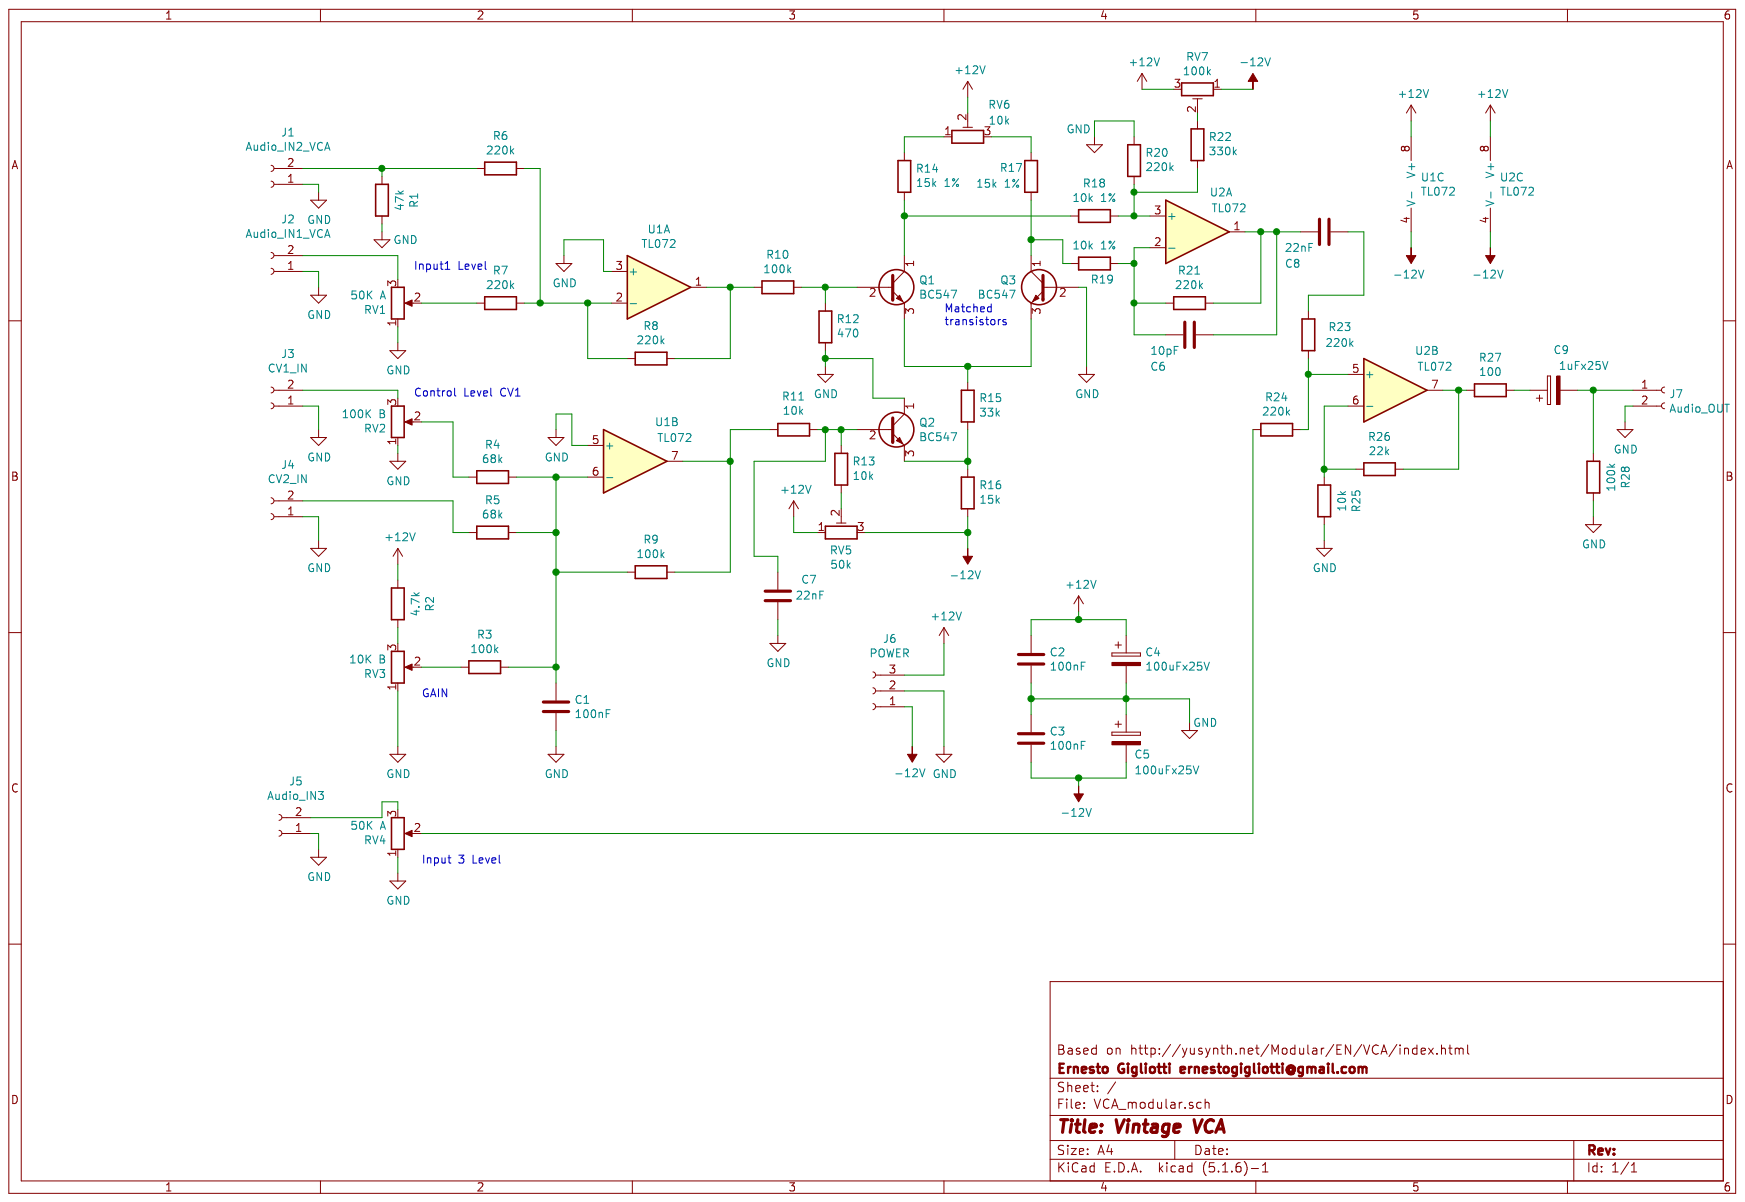
[picture p65: page 1]
