ernesto-g/modular-synth/FINISHED/VCO/VCO_Modular_PCB/DIY/PCB_components.pdf

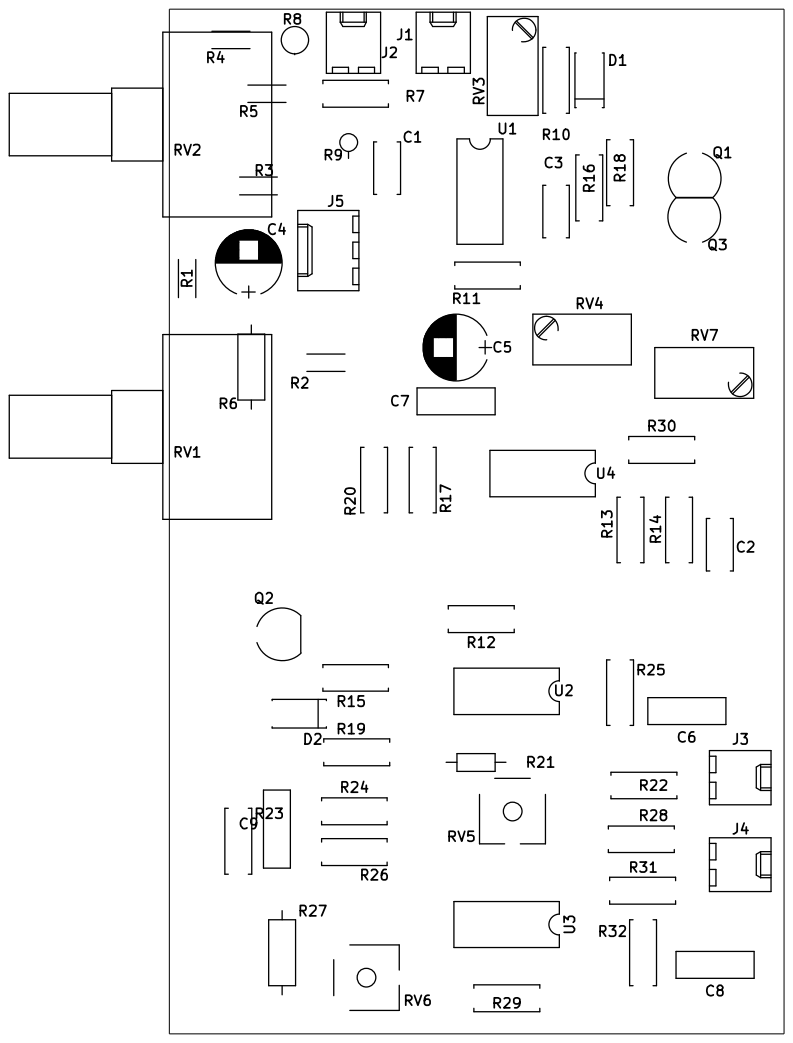
[picture p66: page 1]
