ernesto-g/modular-synth/FINISHED/VCO/VCO_Modular_PCB/DIY/Schematic.pdf

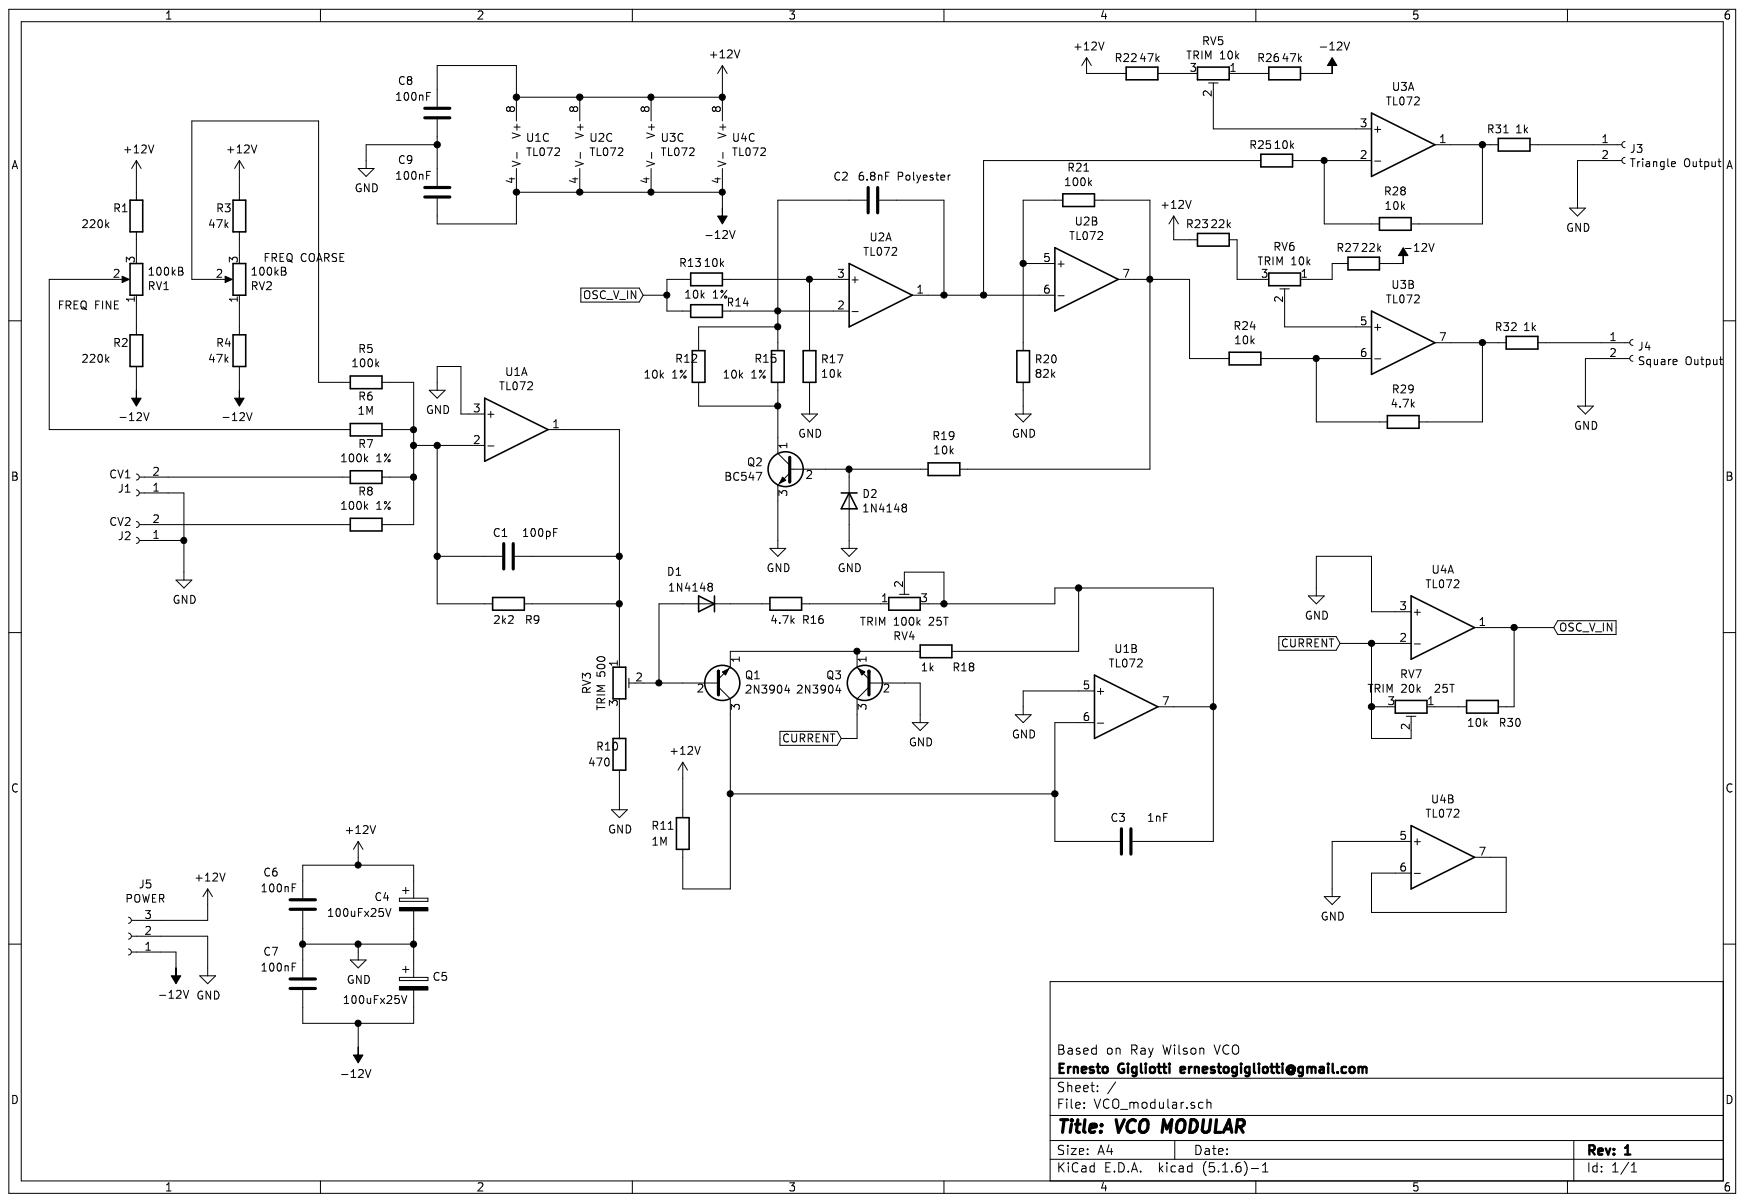
[picture p67: page 1]
