ernesto-g/modular-synth/FINISHED/VCF/VCF_modular_PCB/DIY/VCF_PCB_bottom.pdf

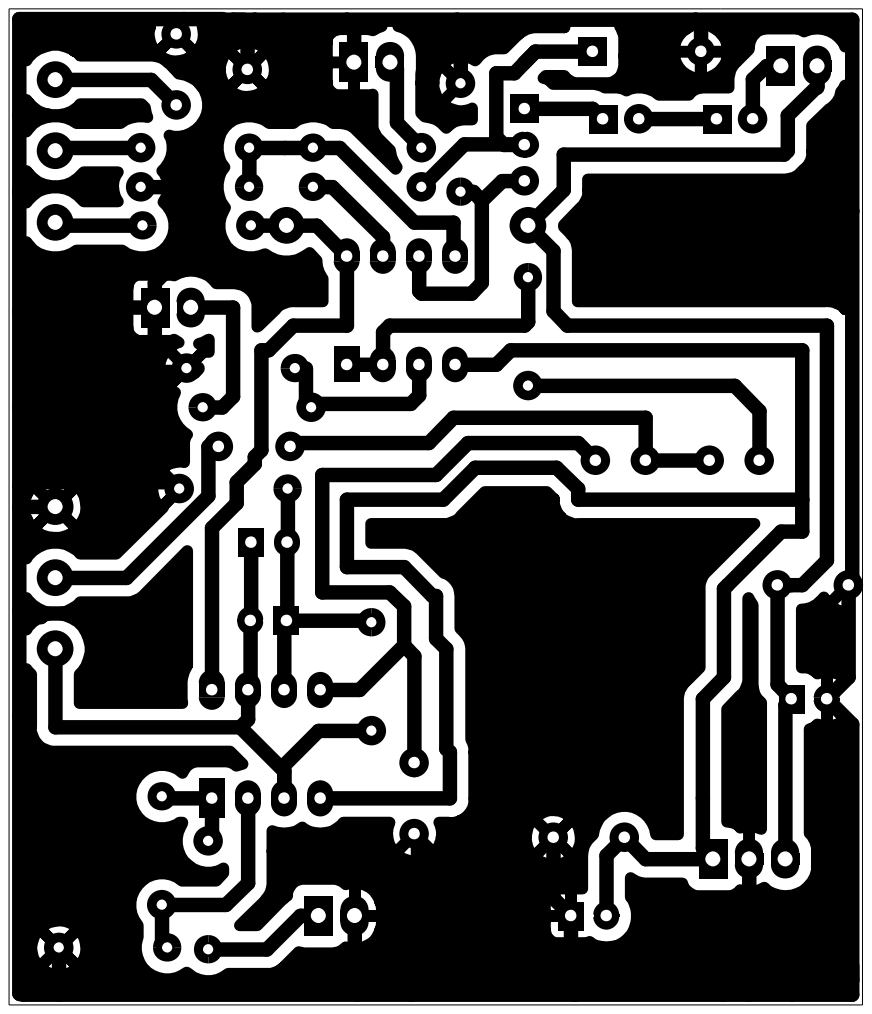
[picture p68: page 1]
