ernesto-g/modular-synth/FINISHED/VCF/VCF_modular_PCB/DIY/VCF_PCB_top.pdf

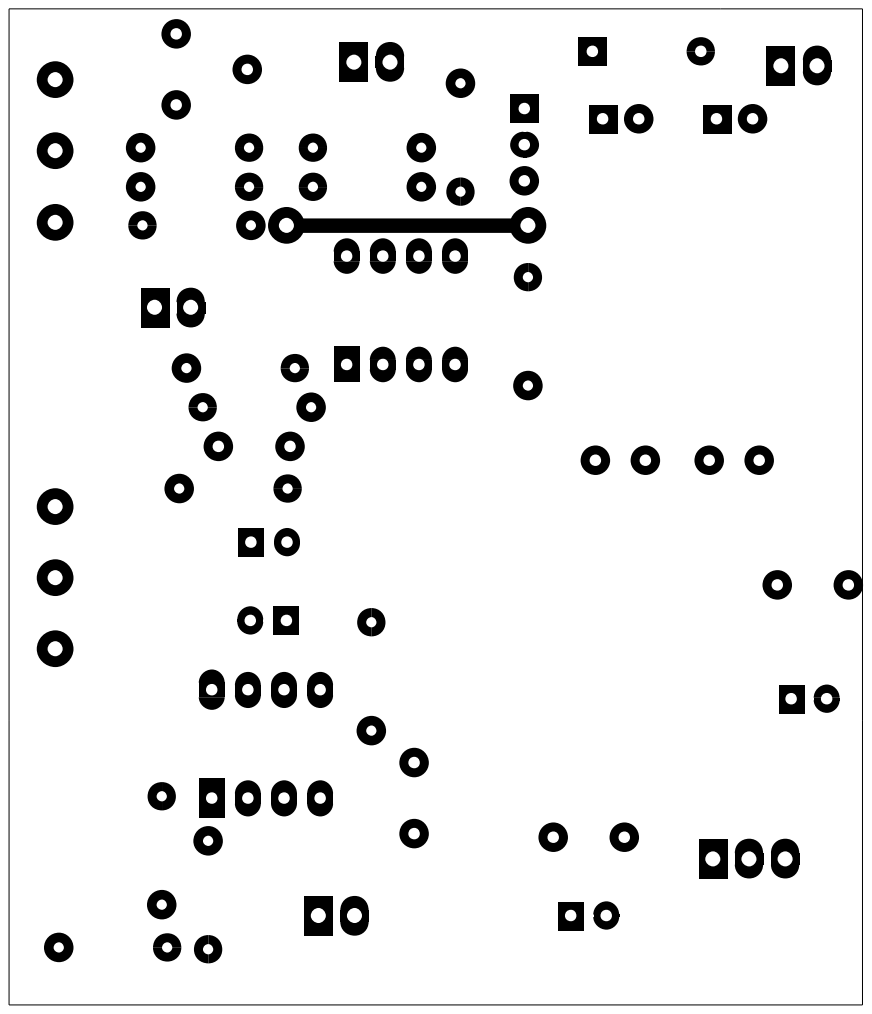
[picture p69: page 1]
