ernesto-g/modular-synth/FINISHED/SIMPLE_SEQUENCER/SIMPLE_SEQUENCER_modular_PCB/DIY/PCB_copper_bottom.pdf

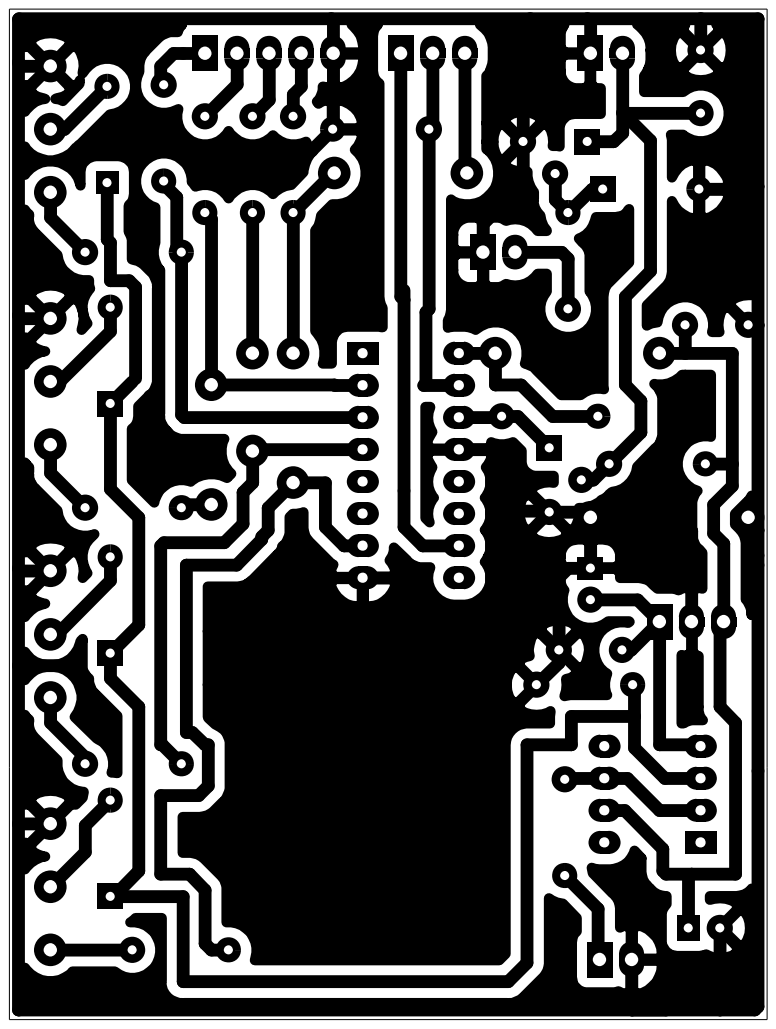
[picture p70: page 1]
