ernesto-g/modular-synth/FINISHED/SIMPLE_SEQUENCER/SIMPLE_SEQUENCER_modular_PCB/DIY/PCB_copper_top.pdf

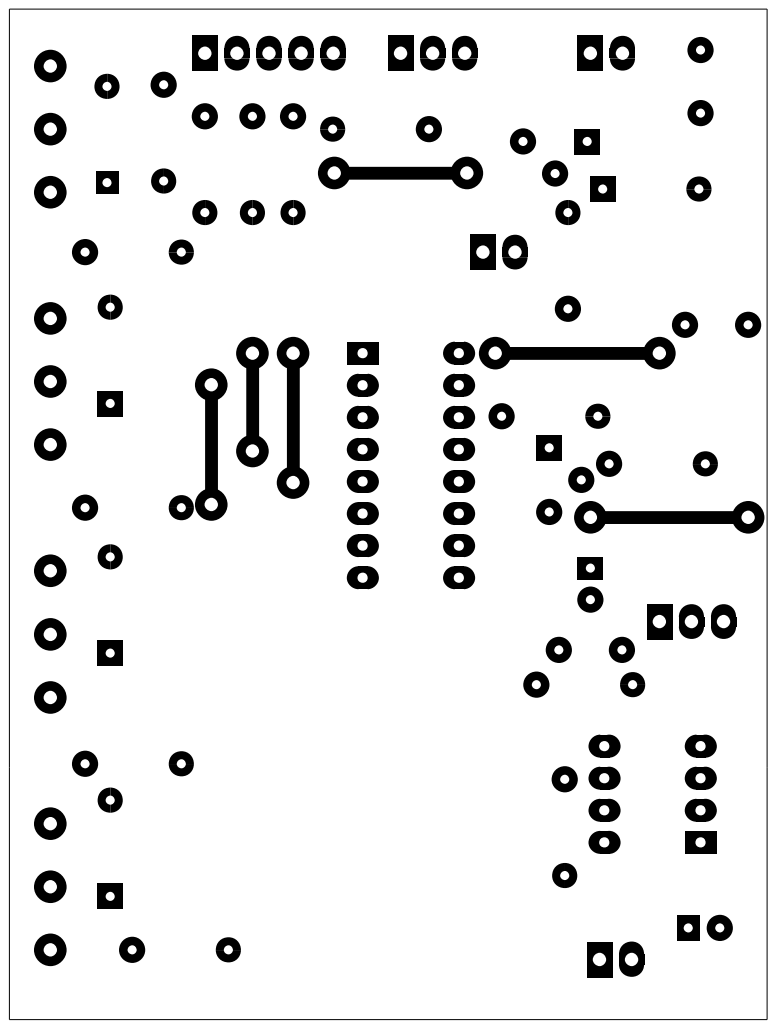
[picture p71: page 1]
