ernesto-g/modular-synth/FINISHED/SIMPLE_SEQUENCER/SIMPLE_SEQUENCER_modular_PCB/DIY/SIMPLE_SEQUENCER_Front_panel.pdf

## SEQ

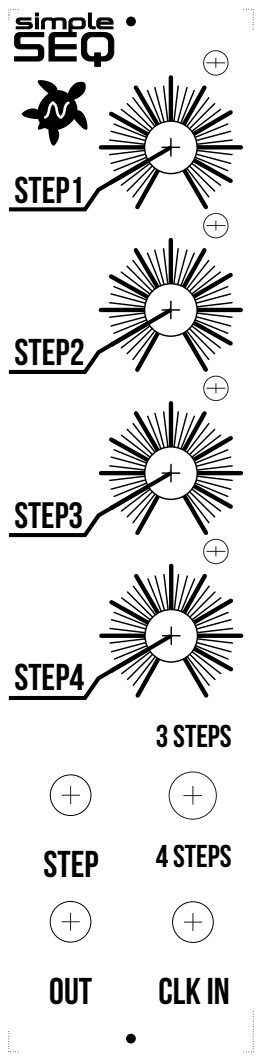
[picture p72: page 1]
STEP1; STEP2; step4; Step3; simple; STEP; OUT; CLK IN; 3 steps; 4 steps
