ernesto-g/modular-synth/FINISHED/SIMPLE_SEQUENCER/SIMPLE_SEQUENCER_modular_PCB/DIY/SIMPLE_SEQUENCER_holes.pdf

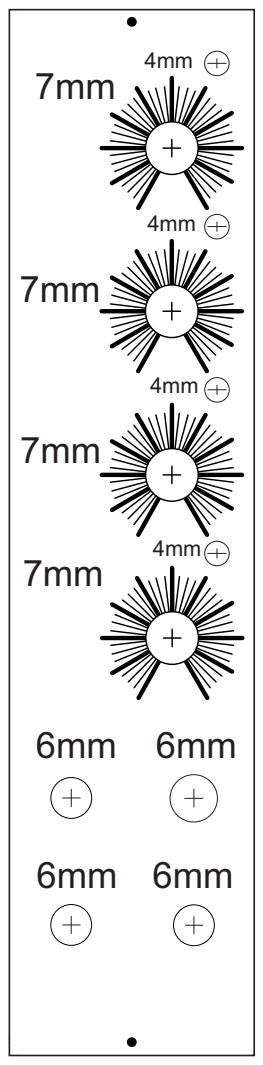
[picture p73: page 1]
