ernesto-g/modular-synth/FINISHED/ATVMixer/ATV_AND_MIXER_modular_PCB/DIY/ATV_MIXER_FRONT_PANEL.pdf

1

2

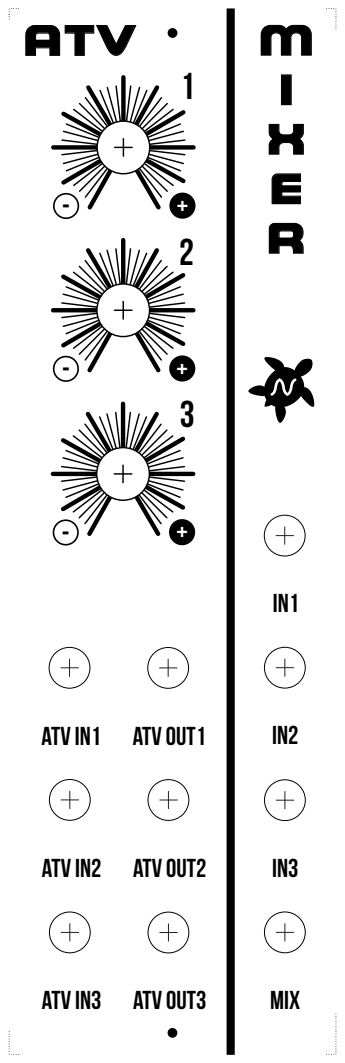
[picture p74: page 1]
MIX; ATV; ATV IN2; ATV IN3; ATV IN1; ATV OUT2; ATV OUT3; ATV OUT1
