ernesto-g/modular-synth/FINISHED/ATVMixer/ATV_AND_MIXER_modular_PCB/DIY/PCB_copper_botom.pdf

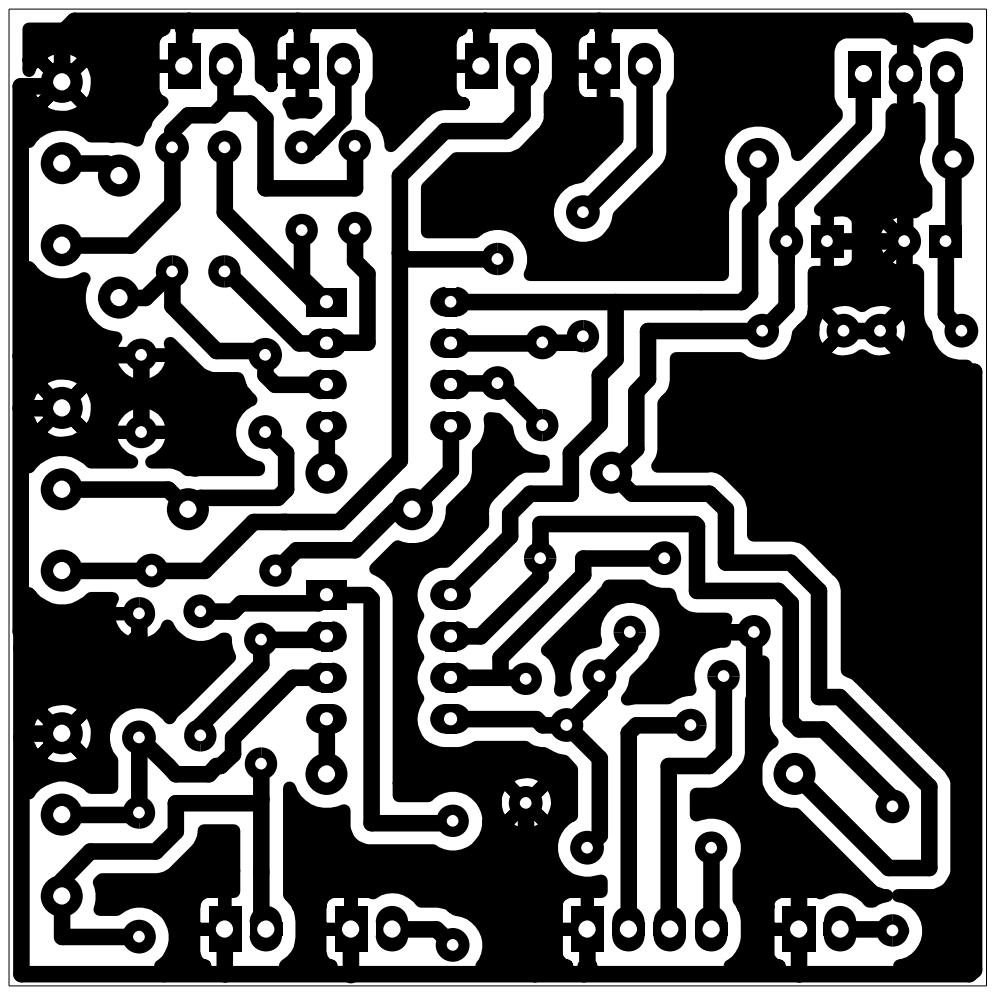
[picture p75: page 1]
