ernesto-g/modular-synth/FINISHED/ATVMixer/ATV_AND_MIXER_modular_PCB/DIY/PCB_copper_front.pdf

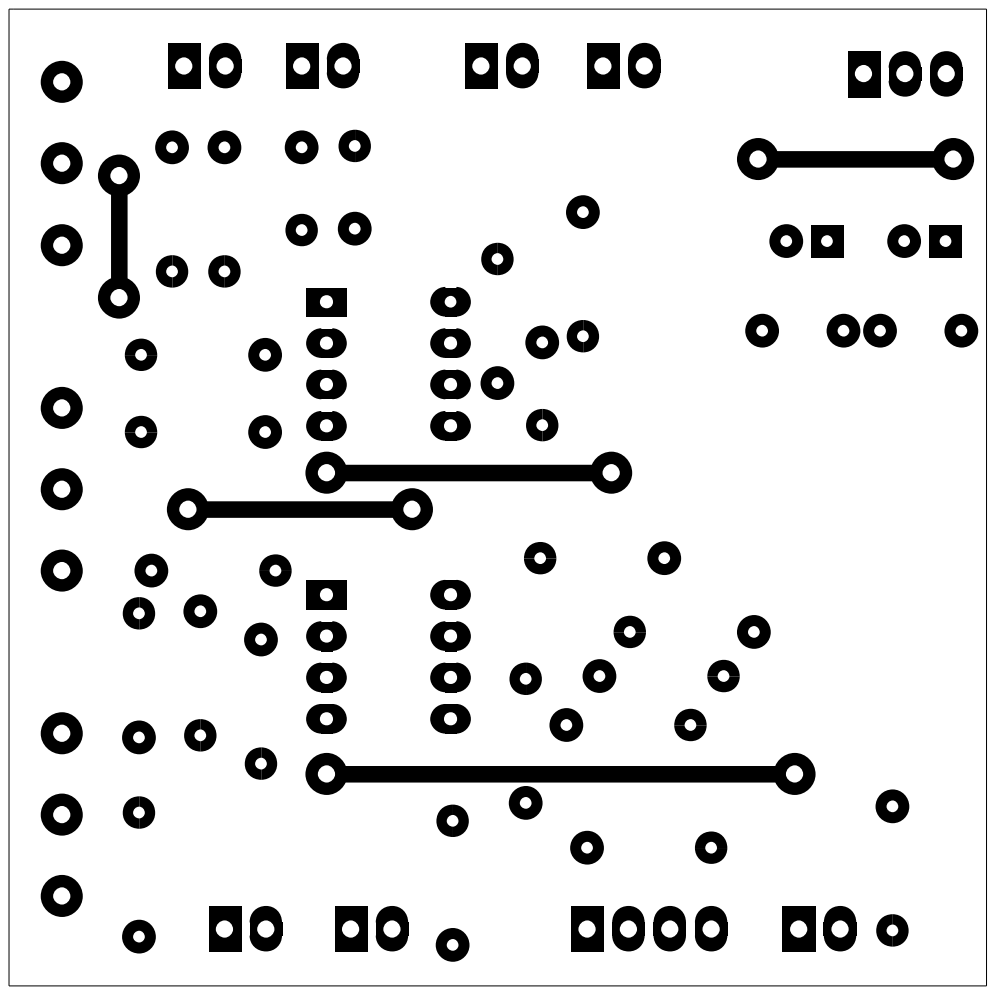
[picture p76: page 1]
