ernesto-g/modular-synth/FINISHED/LFOx3/LFO_modular_PCB/DIY/LFO_X3_FRONT_PANEL.pdf

# LFO

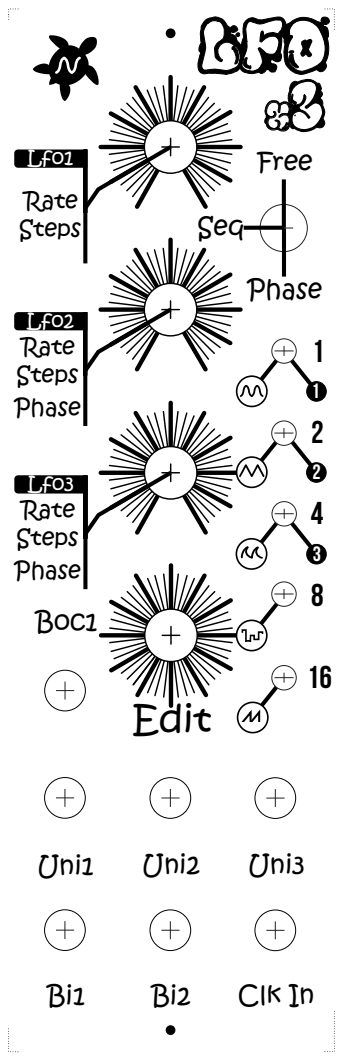
[picture p77: page 1]
Uni1; Uni2; Uni3; Clk In; Edit; Free; Phase; Seq; Rate Steps; Lfo1; Rate Steps Phase; Lfo2; Lfo3; Boc1
