ernesto-g/modular-synth/FINISHED/LFOx3/LFO_modular_PCB/DIY/LFO_X3_FRONT_PANEL_HOLES.pdf

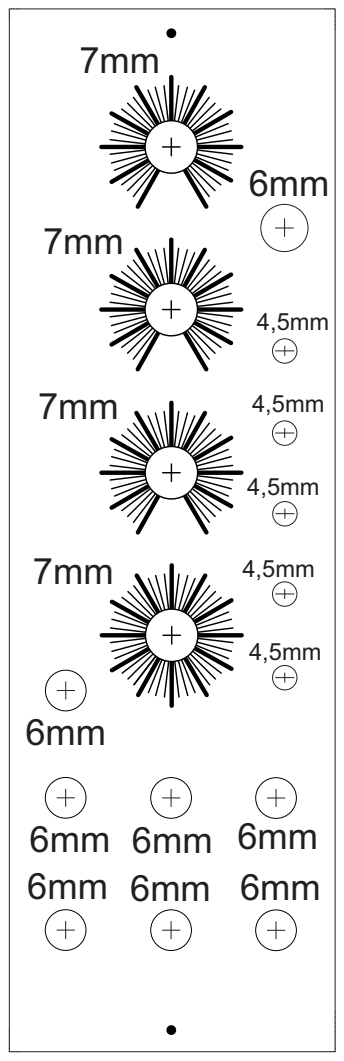
[picture p78: page 1]
