ernesto-g/modular-synth/FINISHED/LFOx3/LFO_modular_PCB/DIY/PCB_copper_botom.pdf

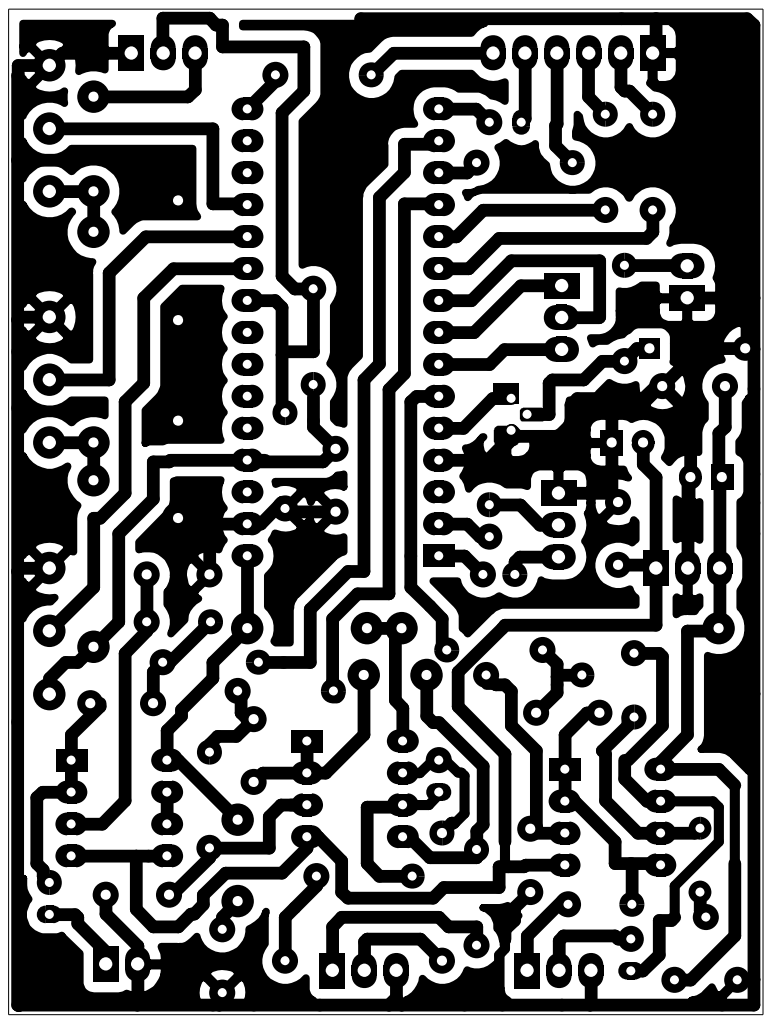
[picture p79: page 1]
