ernesto-g/modular-synth/FINISHED/LFOx3/LFO_modular_PCB/DIY/PCB_copper_front.pdf

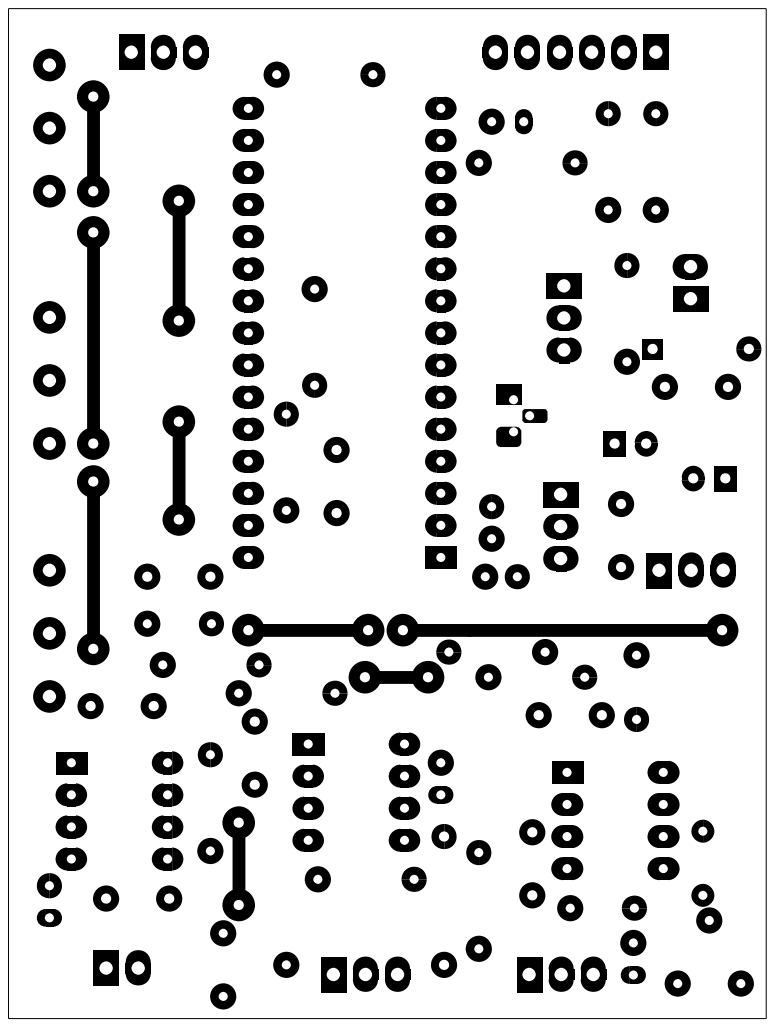
[picture p80: page 1]
