ernesto-g/modular-synth/FINISHED/SOUND_SOURCE/SOUND_SOURCE_modular_PCB/DIY/PCB_copper_botom.pdf

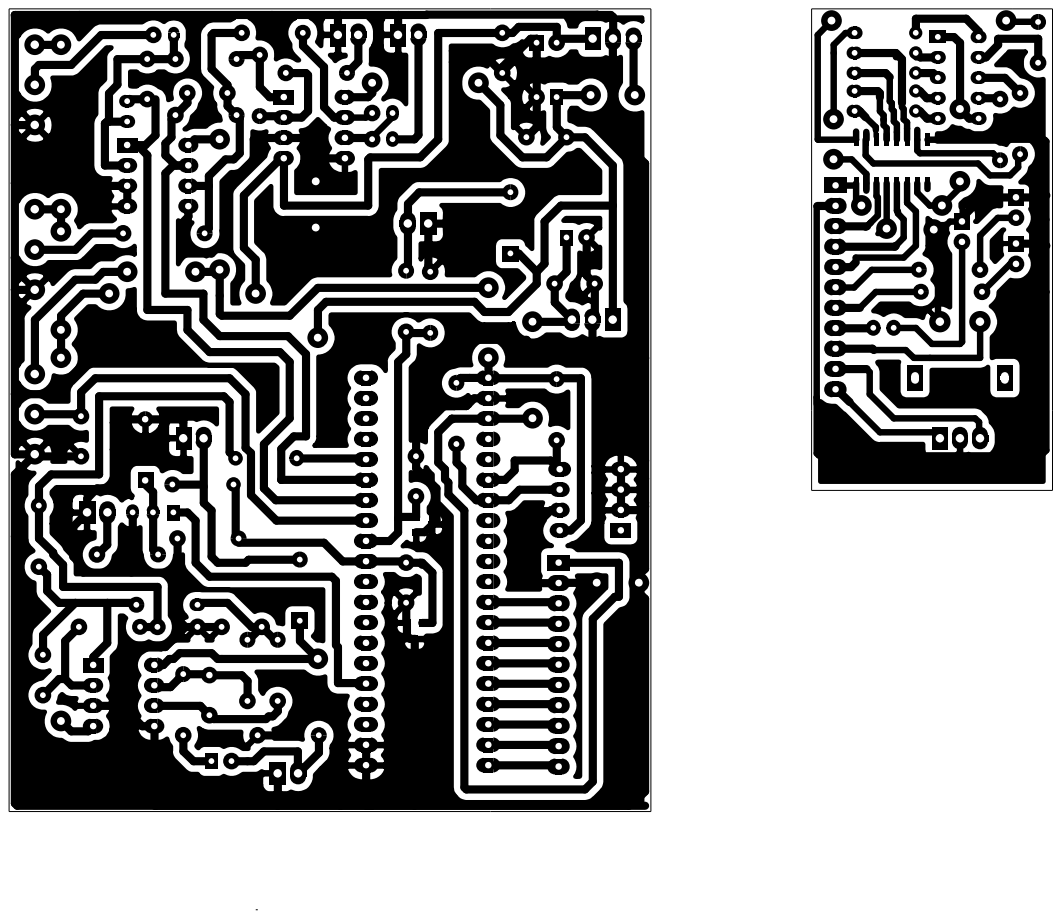
[picture p81: page 1]
