ernesto-g/modular-synth/FINISHED/SOUND_SOURCE/SOUND_SOURCE_modular_PCB/DIY/PCB_copper_front.pdf

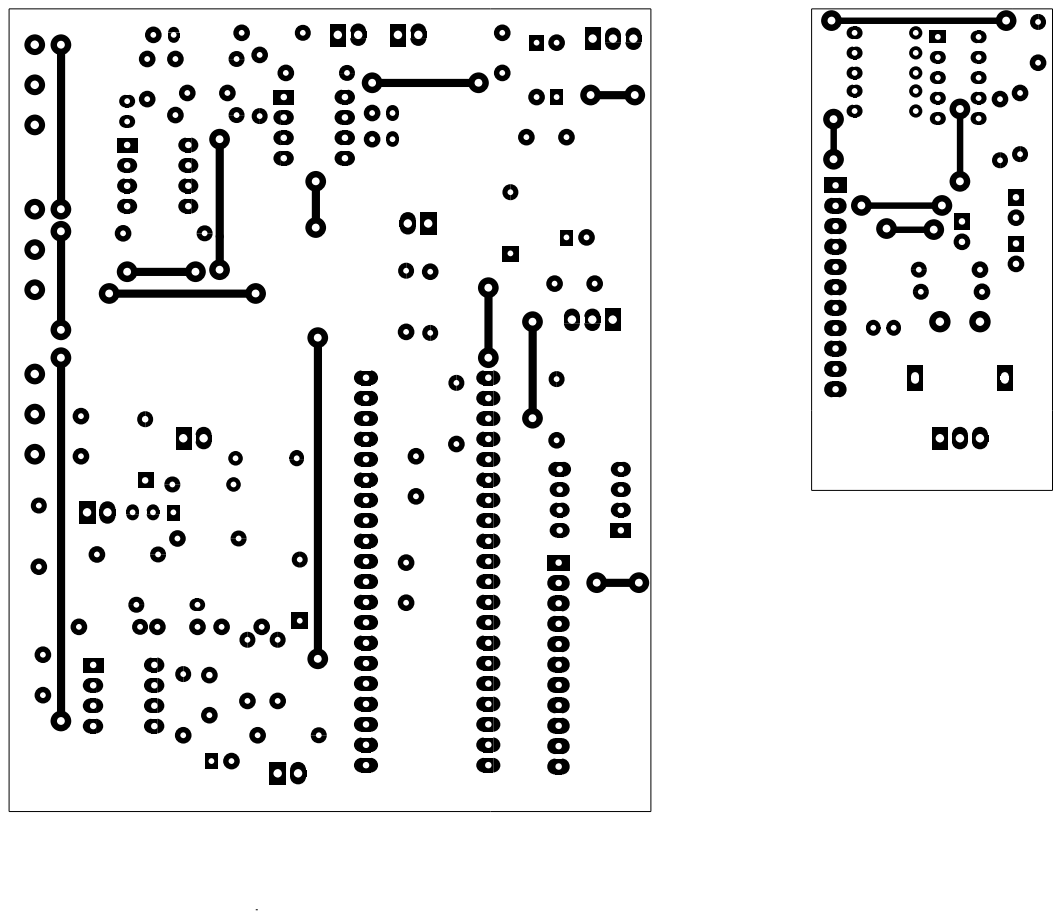
[picture p82: page 1]
