ernesto-g/modular-synth/FINISHED/SOUND_SOURCE/SOUND_SOURCE_modular_PCB/DIY/SOUND_SOURCE_FRONT_PANEL.pdf

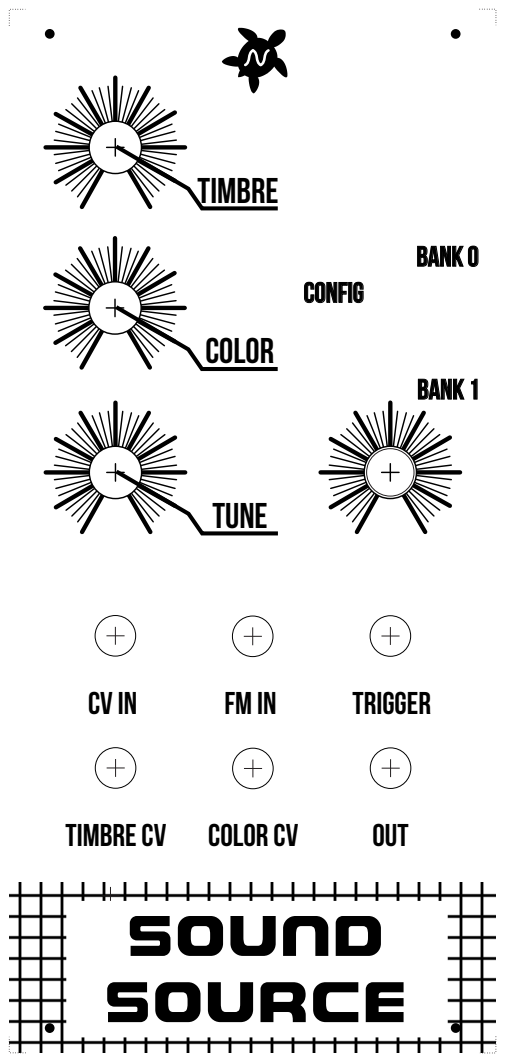
[picture p83: page 1]
BANK 0; CONFIG; BANK 1; SOUND; SOURCE; TIMBRE CV; COLOR CV; TRIGGER; OUT; TIMBRE; COLOR; TUNE
