ernesto-g/modular-synth/FINISHED/SOUND_SOURCE/SOUND_SOURCE_modular_PCB/DIY/SOUND_SOURCE_FRONT_PANEL_holes.pdf

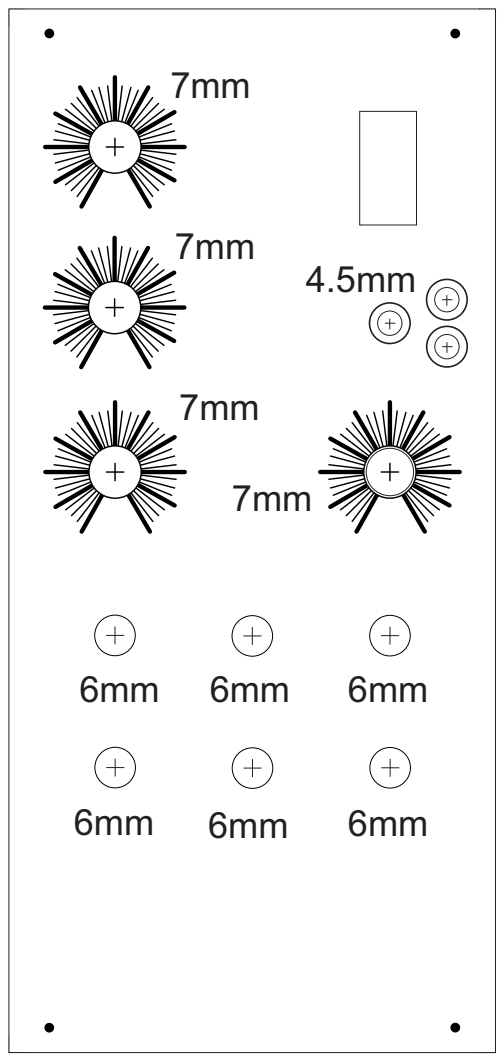
[picture p84: page 1]
