ernesto-g/modular-synth/FINISHED/IOS/IOS_modular_PCB/DIY/IOS_FRONT_PANEL.pdf

### IOs

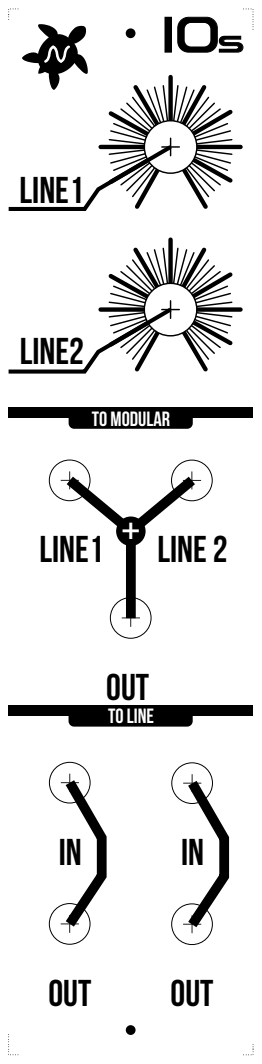
[picture p85: page 1]
LINE1; LINE2; OUT; LINE 2; TO LINE; TO MODULAR
