ernesto-g/modular-synth/FINISHED/IOS/IOS_modular_PCB/DIY/IOS_FRONT_PANEL_holes.pdf

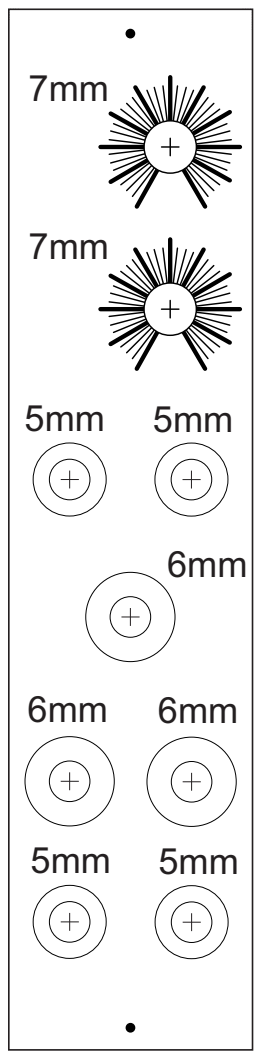
[picture p86: page 1]
