ernesto-g/modular-synth/FINISHED/IOS/IOS_modular_PCB/DIY/PCB_copper_botom.pdf

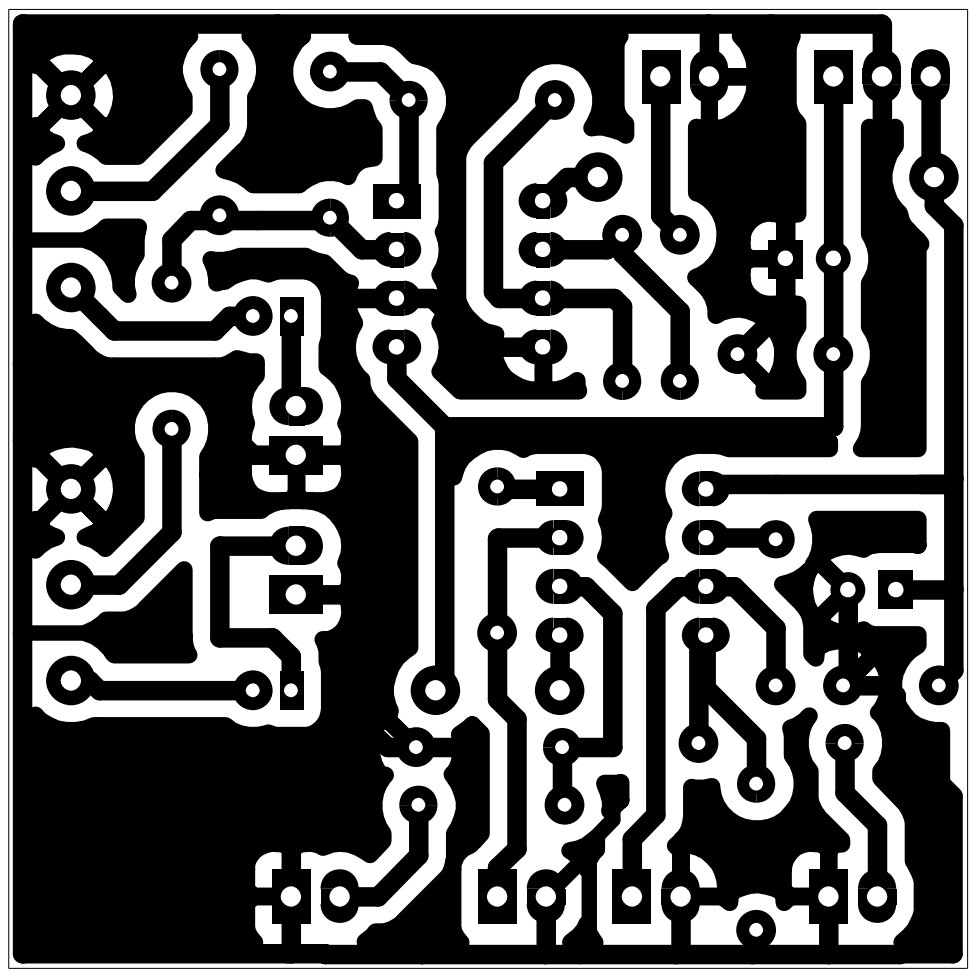
[picture p87: page 1]
