ernesto-g/modular-synth/FINISHED/IOS/IOS_modular_PCB/DIY/PCB_copper_front.pdf

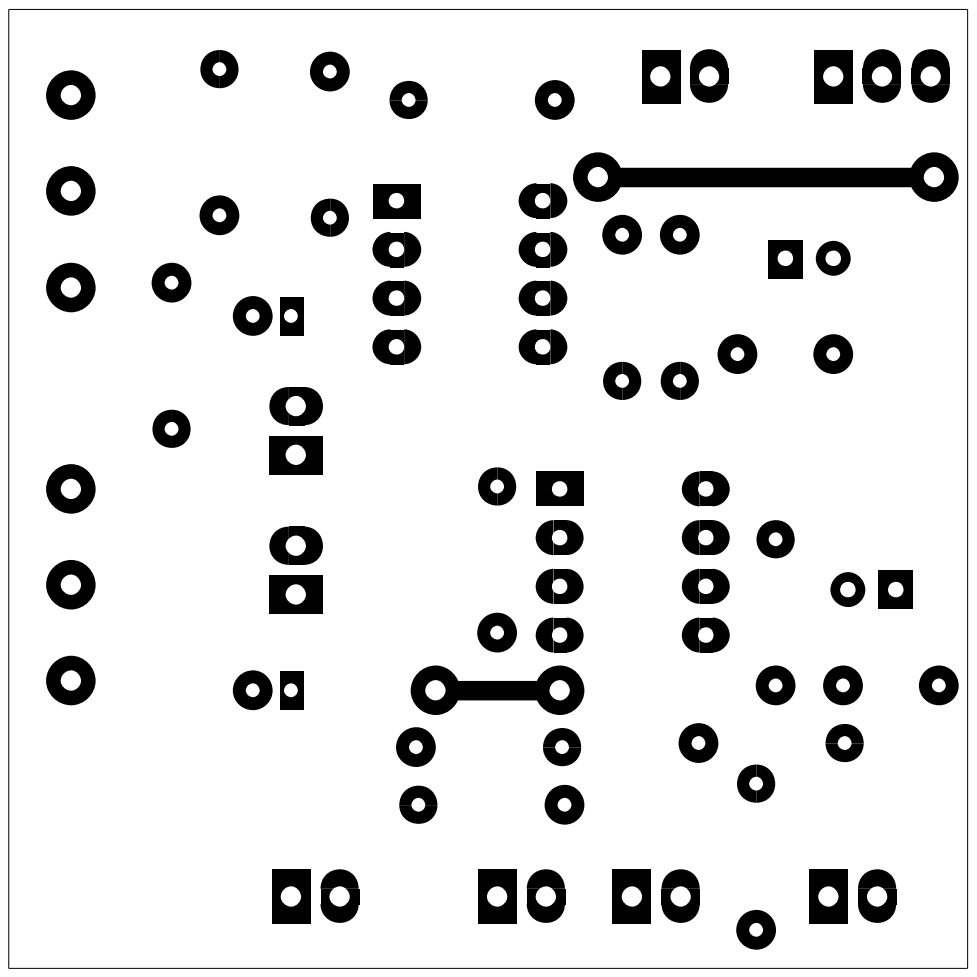
[picture p88: page 1]
