ernesto-g/modular-synth/FINISHED/SEQUENCER/SEQUENCER_modular_PCB/DIY/PCB_copper_botom.pdf

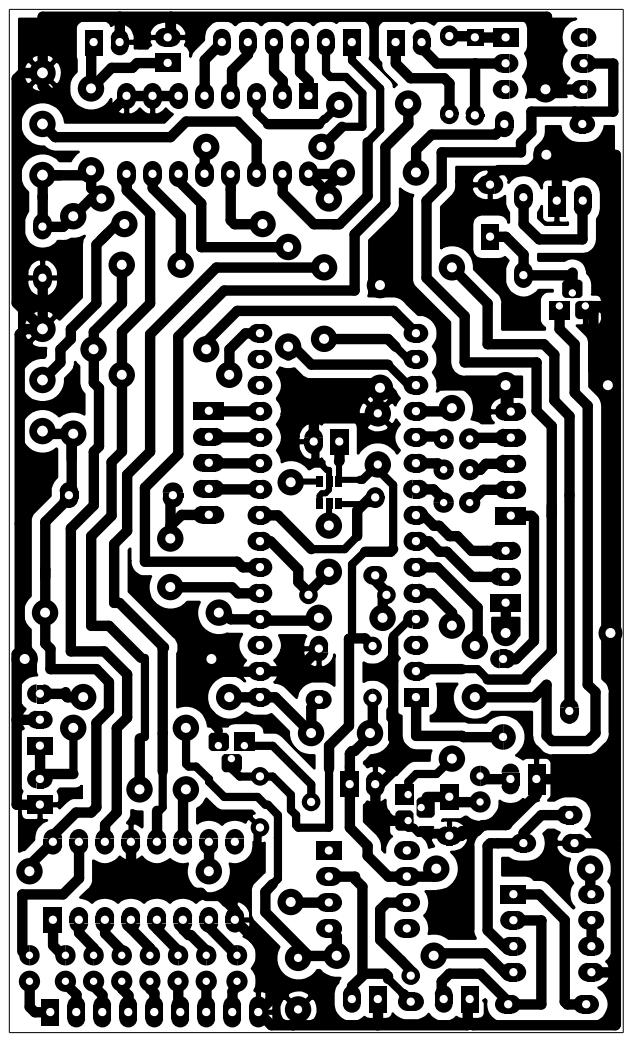
[picture p89: page 1]
