ernesto-g/modular-synth/FINISHED/SEQUENCER/SEQUENCER_modular_PCB/DIY/PCB_copper_front.pdf

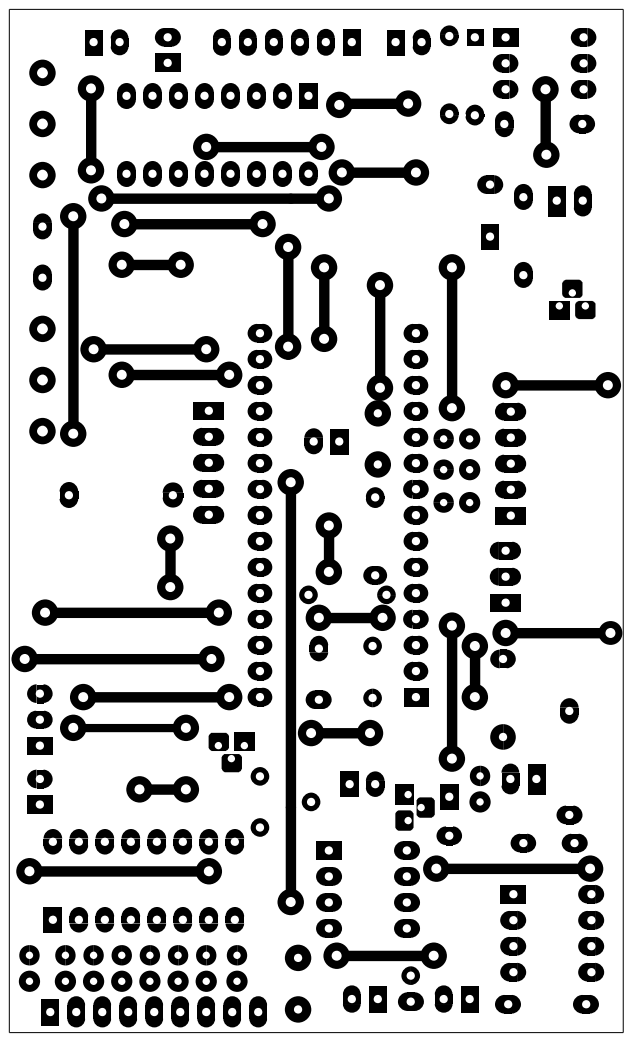
[picture p90: page 1]
