ernesto-g/modular-synth/FINISHED/SEQUENCER/SEQUENCER_modular_PCB/DIY/SEQ_FRONT_PANEL_holes.pdf

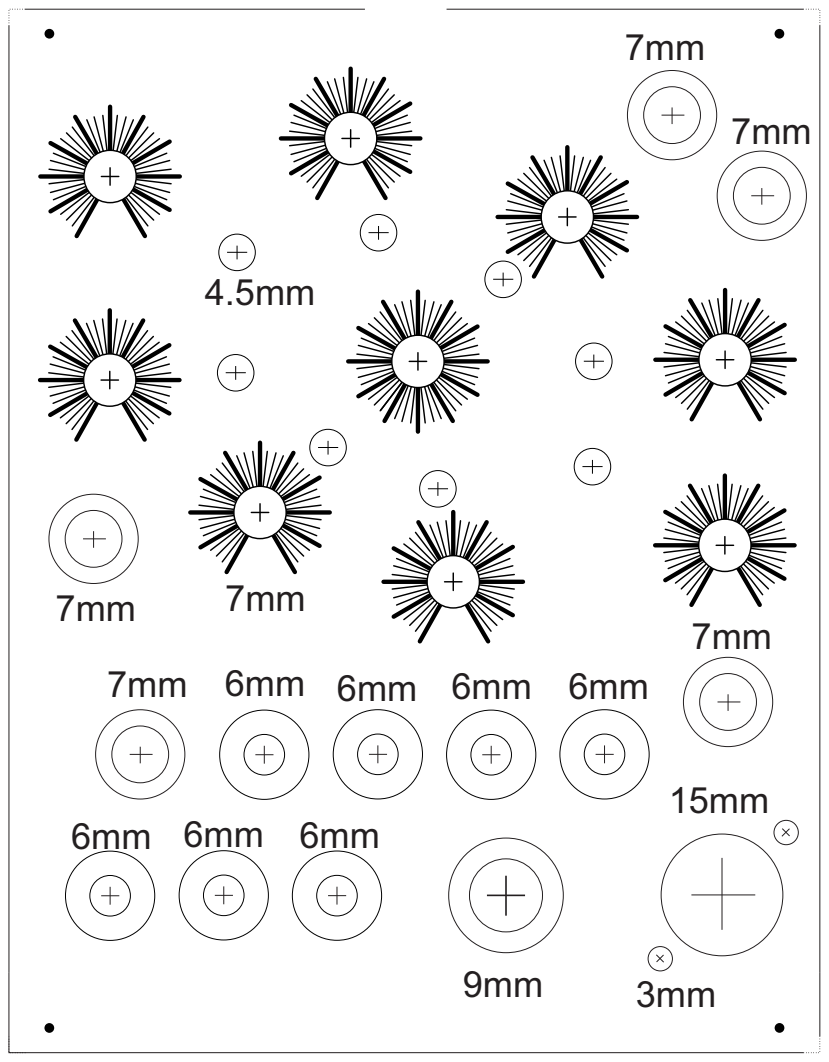
[picture p91: page 1]
