ernesto-g/modular-synth/FINISHED/SLEW_LIMITER/SLEW_LIMITER_modular_PCB/DIY/PCB_copper_botom.pdf

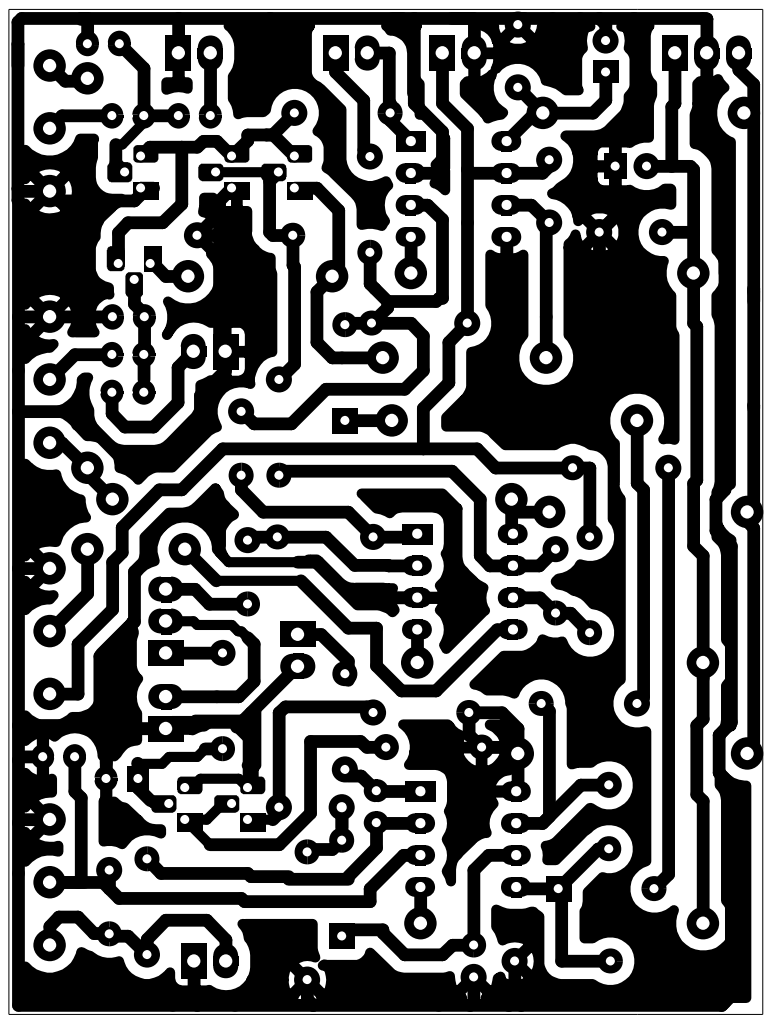
[picture p92: page 1]
