ernesto-g/modular-synth/FINISHED/SLEW_LIMITER/SLEW_LIMITER_modular_PCB/DIY/PCB_copper_front.pdf

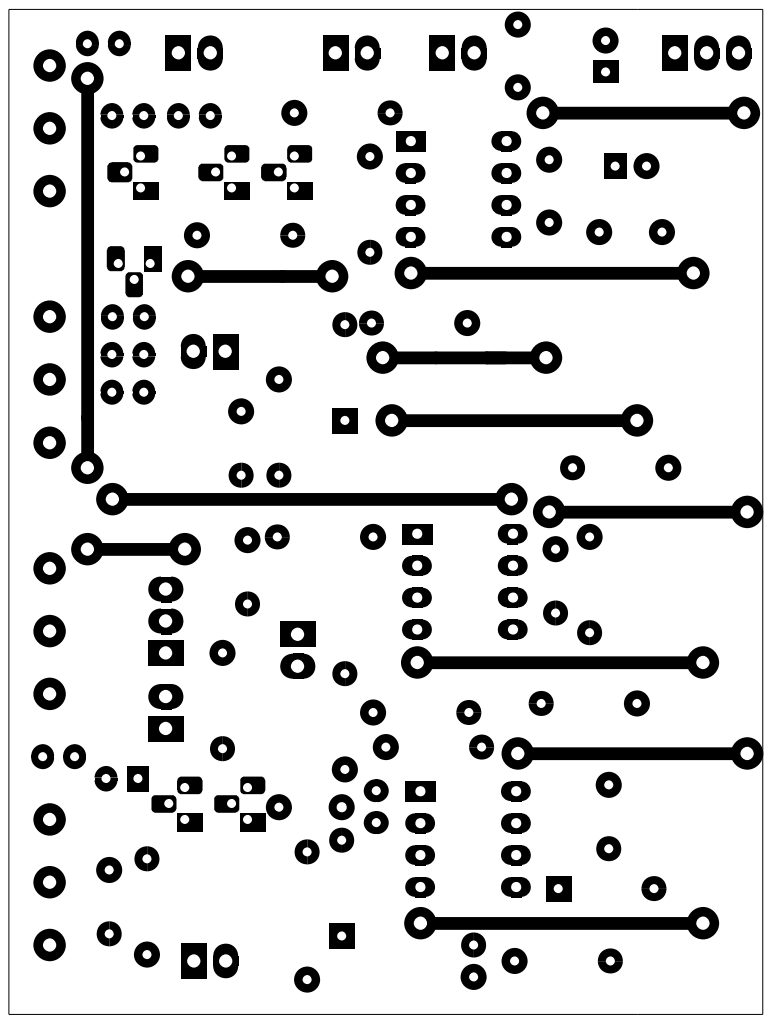
[picture p93: page 1]
