ernesto-g/modular-synth/FINISHED/SLEW_LIMITER/SLEW_LIMITER_modular_PCB/DIY/SLEW_LIMITER_FRONT_PANEL.pdf

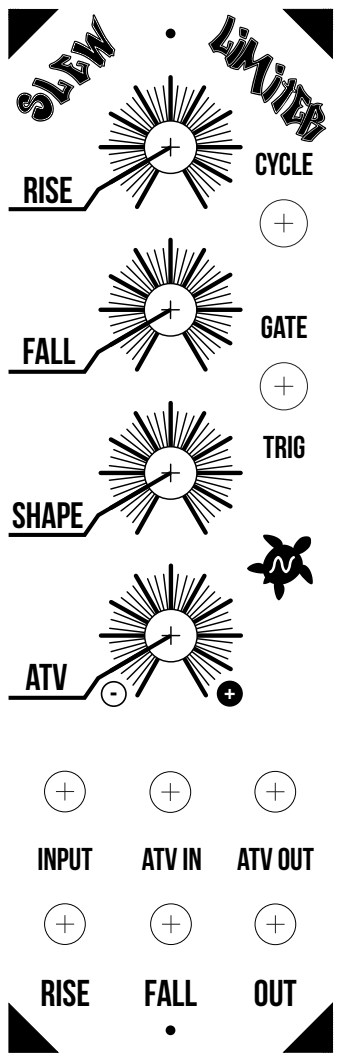
[picture p94: page 1]
RISE; FALL; ATV; INPUT; ATV IN; ATV OUT; OUT; SHAPE; LIMITER; SLEW; CYCLE; GATE; TRIG
