ernesto-g/modular-synth/FINISHED/SLEW_LIMITER/SLEW_LIMITER_modular_PCB/DIY/SLEW_LIMITER_FRONT_PANEL_holes.pdf

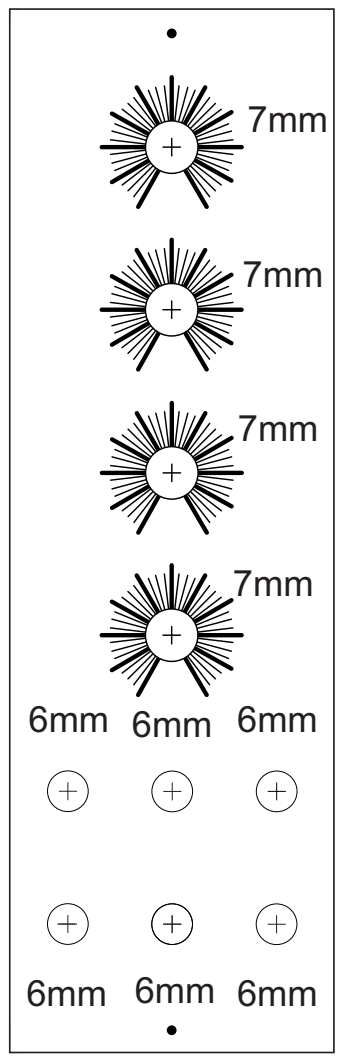
[picture p95: page 1]
