ernesto-g/modular-synth/FINISHED/VCA/VCA_modular_PCB/DIY/PCB_copper_botom.pdf

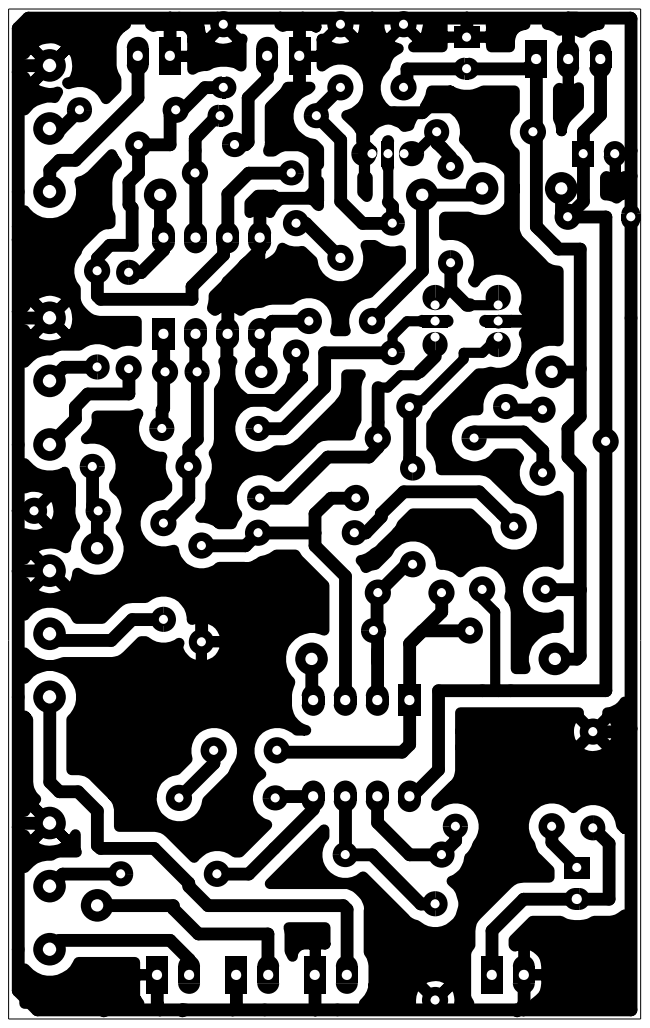
[picture p96: page 1]
