ernesto-g/modular-synth/FINISHED/VCA/VCA_modular_PCB/DIY/PCB_copper_front.pdf

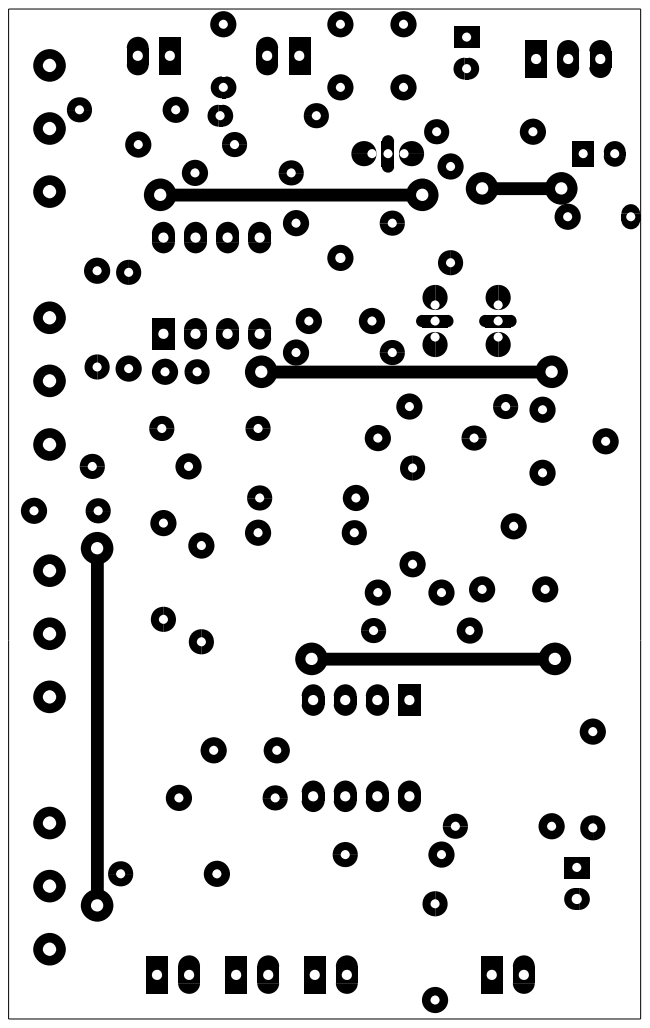
[picture p97: page 1]
