ernesto-g/modular-synth/FINISHED/VCA/VCA_modular_PCB/DIY/VCA_FRONT_PANEL.pdf

cv1

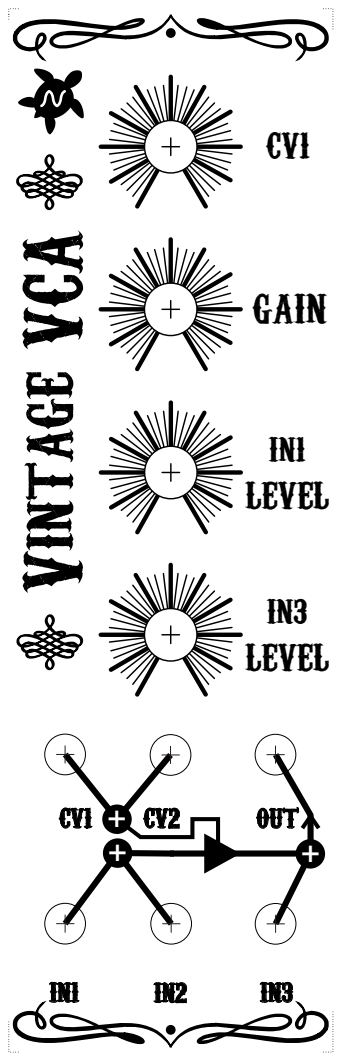
[picture p98: page 1]
GAIN; LEVEL; out; Vintage VCA
