ernesto-g/modular-synth/FINISHED/VCA/VCA_modular_PCB/DIY/VCA_FRONT_PANEL_holes.pdf

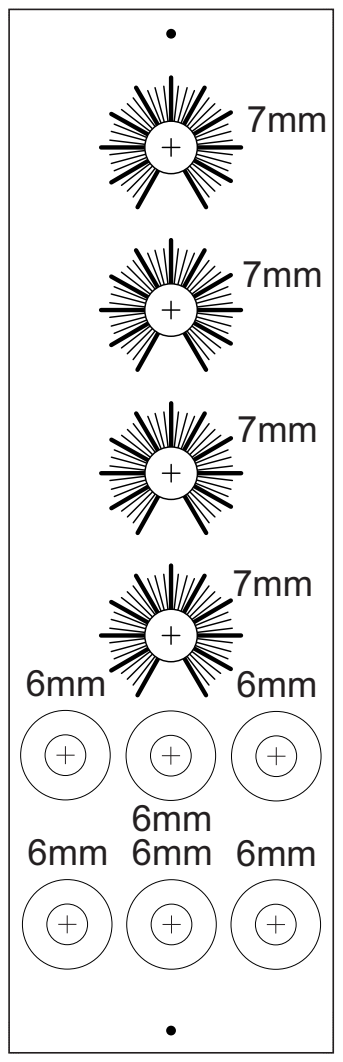
[picture p99: page 1]
