ernesto-g/modular-synth/FINISHED/VCO/VCO_Modular_PCB/DIY/PCB_copper_botom.pdf

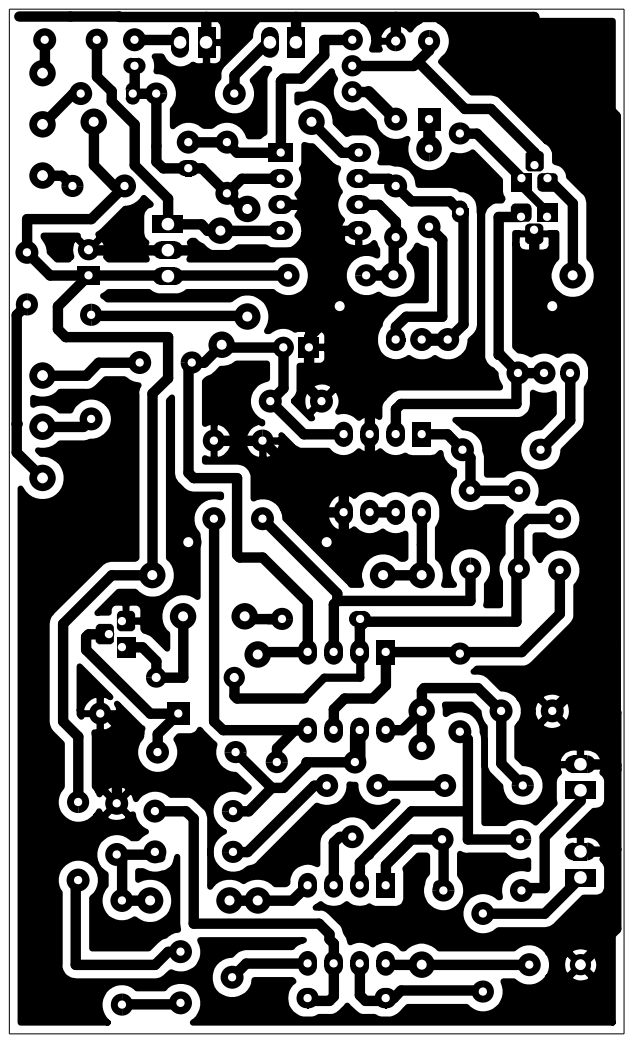
[picture p100: page 1]
