ernesto-g/modular-synth/FINISHED/VCO/VCO_Modular_PCB/DIY/PCB_copper_front.pdf

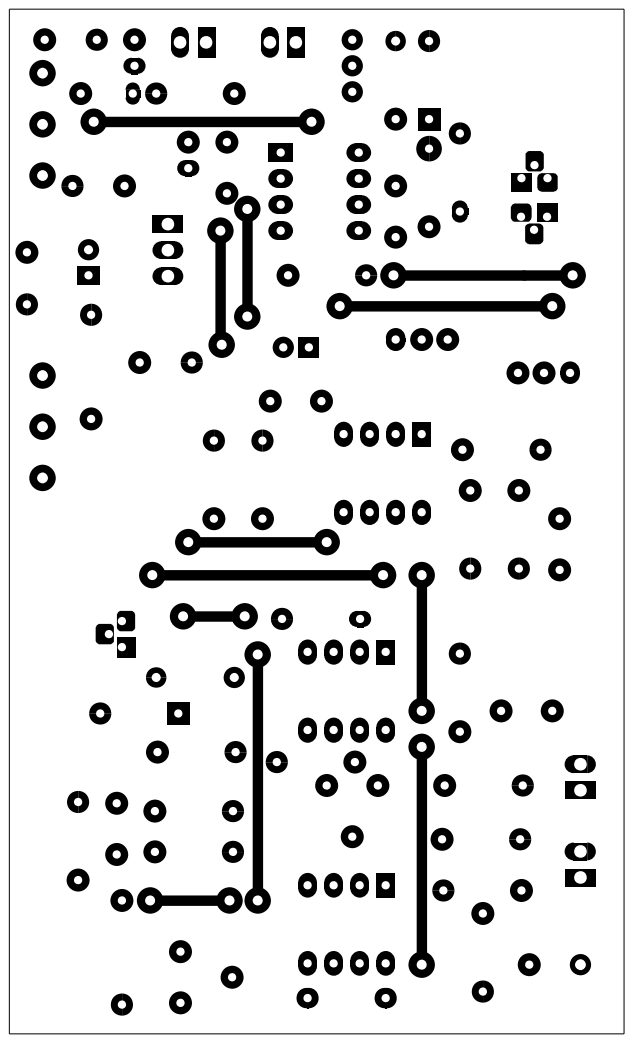
[picture p101: page 1]
