ernesto-g/modular-synth/FINISHED/VCO/VCO_Modular_PCB/DIY/VCO_FRONT_PANEL.pdf

# COARSE

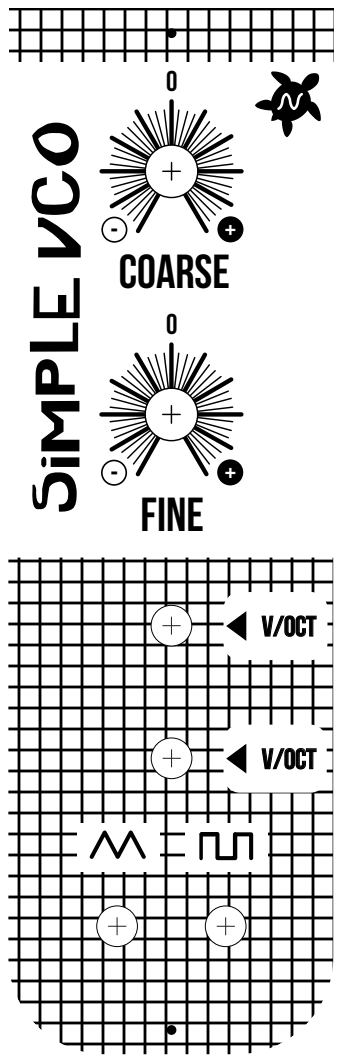
[picture p102: page 1]
FINE; Simple VCO; V/OCT
