ernesto-g/modular-synth/FINISHED/VCO/VCO_Modular_PCB/DIY/VCO_FRONT_PANEL_holes.pdf

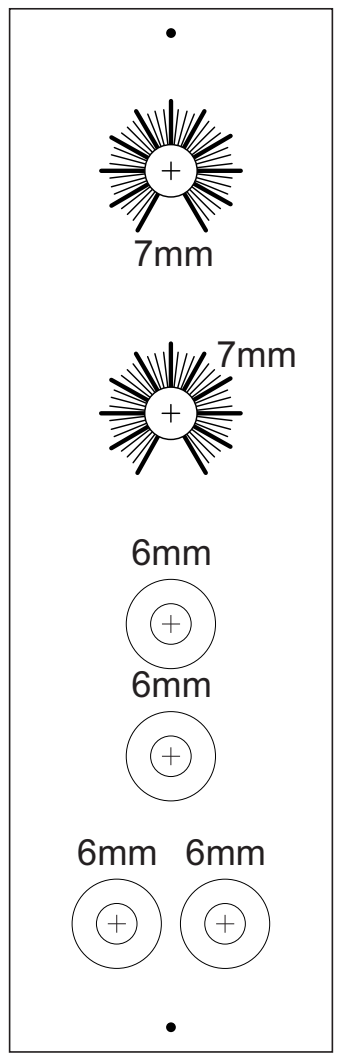
[picture p103: page 1]
