ernesto-g/modular-synth/FINISHED/POWER_SUPPLY/DIY/PCB_components.pdf

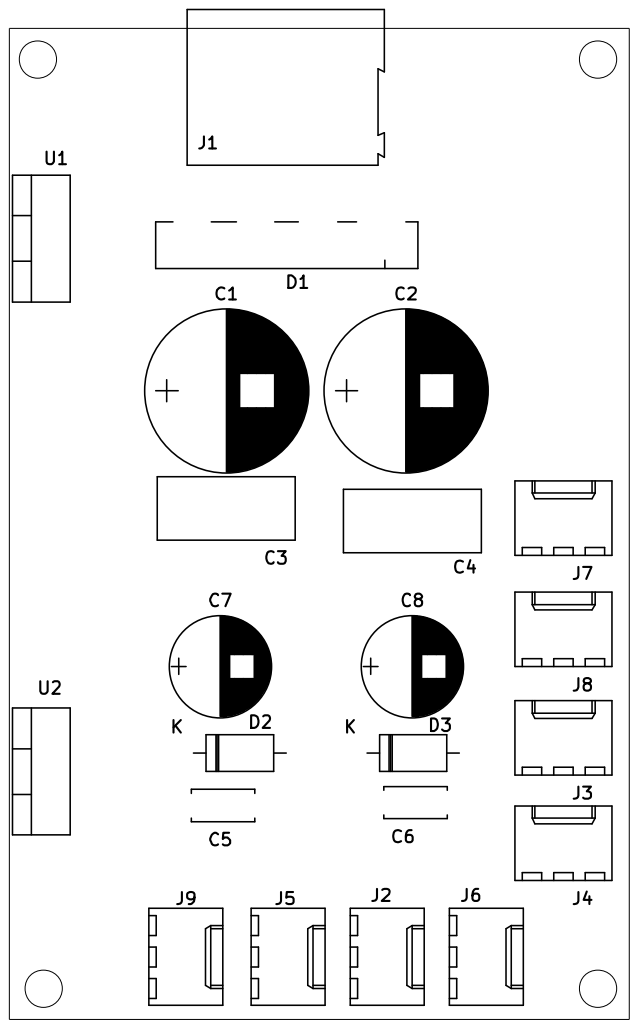
[picture p104: page 1]
