ernesto-g/modular-synth/FINISHED/POWER_SUPPLY/DIY/Schematic.pdf

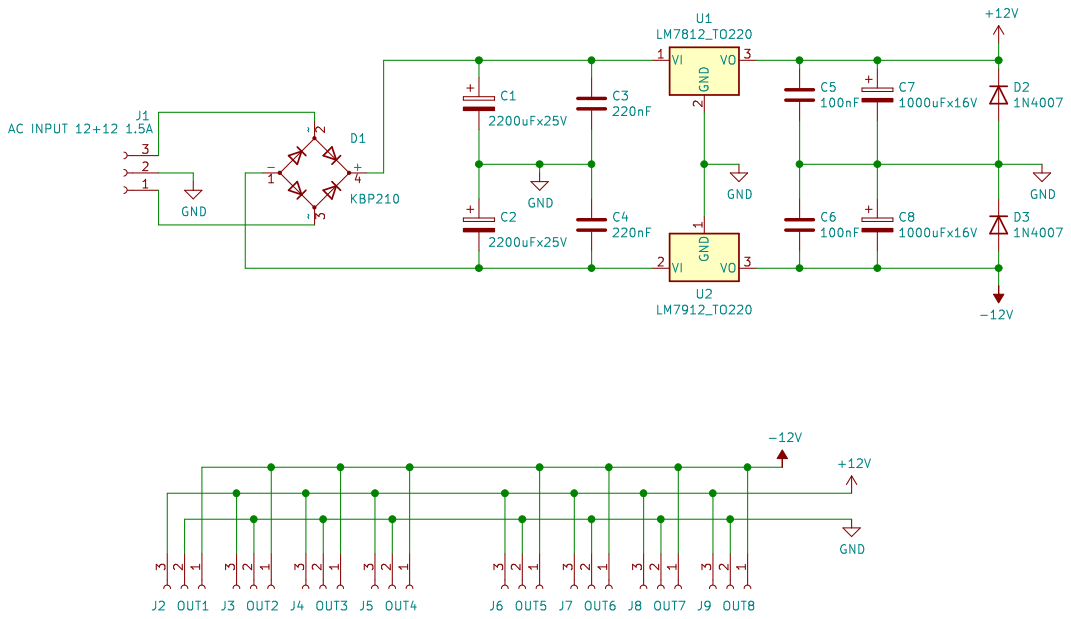
[picture p105: page 1]
