ernesto-g/modular-synth/FINISHED/POWER_SUPPLY/DIY/PCB_copper_front.pdf

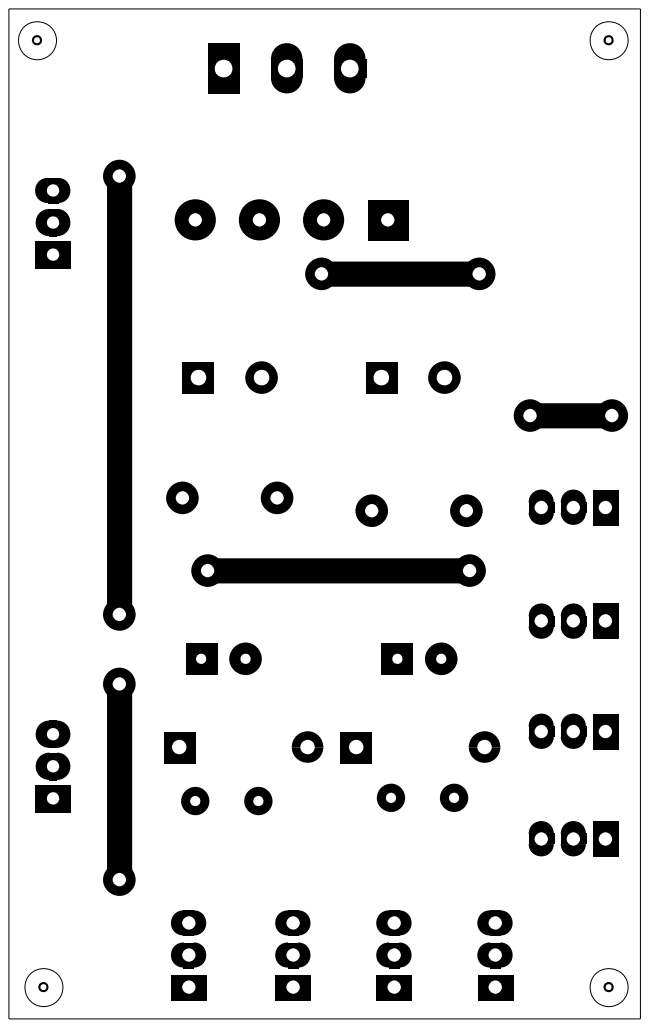
[picture p106: page 1]
