ernesto-g/modular-synth/FINISHED/POWER_SUPPLY/DIY/PCB_copper_botom.pdf

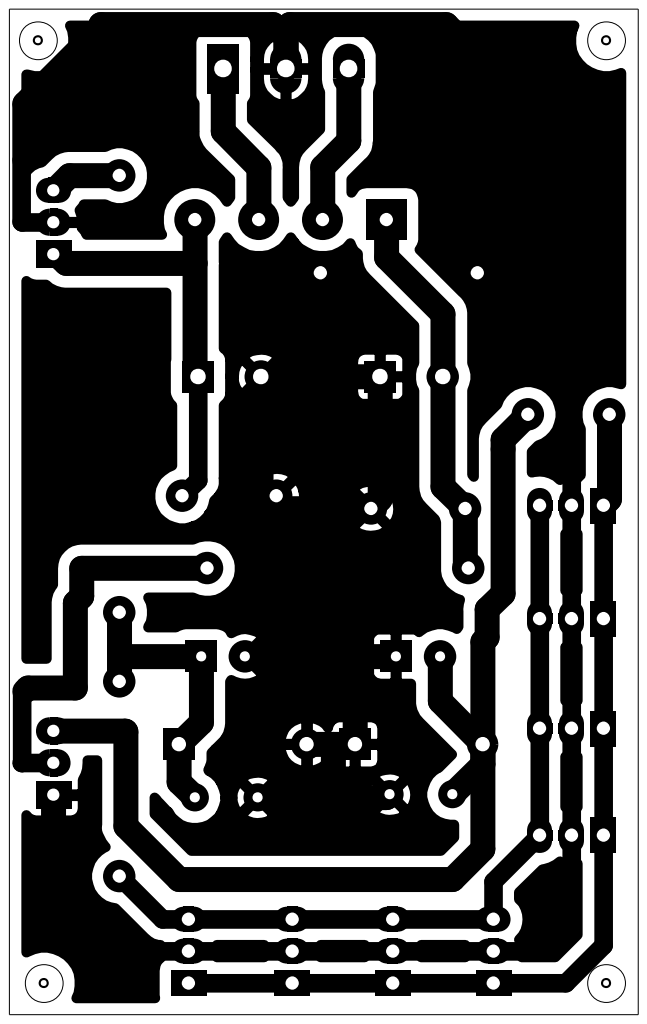
[picture p107: page 1]
