ernesto-g/modular-synth/FINISHED/LFOx3/Firmware/Main.ino/Waveforms.cpp

#include <Arduino.h>
#include "Waveforms.h"


const unsigned char SINETABLE[TABLE_SIZE] PROGMEM = {0x80,0x80,0x80,0x81,0x81,0x81,0x82,0x82,0x83,0x83,0x83,0x84,0x84,0x85,0x85,0x85,0x86,0x86,0x87,0x87,0x87,0x88,0x88,0x88,0x89,0x89,0x8a,0x8a,0x8a,0x8b,0x8b,0x8c,0x8c,0x8c,0x8d,0x8d,0x8e,0x8e,0x8e,0x8f,0x8f,0x8f,0x90,0x90,0x91,0x91,0x91,0x92,0x92,0x93,0x93,0x93,0x94,0x94,0x95,0x95,0x95,0x96,0x96,0x96,0x97,0x97,0x98,0x98,
0x98,0x99,0x99,0x9a,0x9a,0x9a,0x9b,0x9b,0x9b,0x9c,0x9c,0x9d,0x9d,0x9d,0x9e,0x9e,0x9e,0x9f,0x9f,0xa0,0xa0,0xa0,0xa1,0xa1,0xa2,0xa2,0xa2,0xa3,0xa3,0xa3,0xa4,0xa4,0xa5,0xa5,0xa5,0xa6,0xa6,0xa6,0xa7,0xa7,0xa7,0xa8,0xa8,0xa9,0xa9,0xa9,0xaa,0xaa,0xaa,0xab,0xab,0xac,0xac,0xac,0xad,0xad,0xad,0xae,0xae,0xae,0xaf,0xaf,0xb0,0xb0,
0xb0,0xb1,0xb1,0xb1,0xb2,0xb2,0xb2,0xb3,0xb3,0xb4,0xb4,0xb4,0xb5,0xb5,0xb5,0xb6,0xb6,0xb6,0xb7,0xb7,0xb7,0xb8,0xb8,0xb8,0xb9,0xb9,0xba,0xba,0xba,0xbb,0xbb,0xbb,0xbc,0xbc,0xbc,0xbd,0xbd,0xbd,0xbe,0xbe,0xbe,0xbf,0xbf,0xbf,0xc0,0xc0,0xc0,0xc1,0xc1,0xc1,0xc2,0xc2,0xc2,0xc3,0xc3,0xc3,0xc4,0xc4,0xc4,0xc5,0xc5,0xc5,0xc6,0xc6,
0xc6,0xc7,0xc7,0xc7,0xc8,0xc8,0xc8,0xc9,0xc9,0xc9,0xca,0xca,0xca,0xcb,0xcb,0xcb,0xcb,0xcc,0xcc,0xcc,0xcd,0xcd,0xcd,0xce,0xce,0xce,0xcf,0xcf,0xcf,0xcf,0xd0,0xd0,0xd0,0xd1,0xd1,0xd1,0xd2,0xd2,0xd2,0xd2,0xd3,0xd3,0xd3,0xd4,0xd4,0xd4,0xd5,0xd5,0xd5,0xd5,0xd6,0xd6,0xd6,0xd7,0xd7,0xd7,0xd7,0xd8,0xd8,0xd8,0xd9,0xd9,0xd9,0xd9,
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
07,4146,4185,4225,4265,4305,4346,4387,4429,4471,4513,4556,4599,4643,4687,4732,4776,4822,4867,4914,4960,5007,5055,5103,5151,5200,5250,5299,5350,5400,5452,5503,5556,5608,5661,5715,5769,5824,5879,5935,5992,6048,6106,6164,6222,6281,6341,6401,6462,6523,6585,6647,6711,6774,6839,6903,6969,7035,7102,7169,7237,7306,7375,7445,7516,7587,7659,7732,7805,7879,7954,8030,8106,8183,8260,8339,8418,8498,8578,8660,8742,8825,8909,8993,9078,9165,9251,9339,9428,9517,9608,9699,9791,9884,9978,10072,10168,10264,10362,10460,10559,10659,10761,10863,10966,11070,11175,11281,11388,11496,11605,11715,11826,11939,12052,12166,12282,12398,12516,12635,12755,12876,12998,13121,13246,13371,13498,13626,13756,13886,14018,14151,14285,14421,14558,14696,14835,14976,15118,15261,15406,15552,15700};
