ernesto-g/modular-synth/FINISHED/LFOx3/Firmware/Main.ino/Ios.h

void ios_init(void);
uint8_t ios_getClkIn(void);
uint16_t ios_getAnalogValue(uint8_t index);
uint8_t ios_getEncoderSw(void);
uint8_t ios_getEncoderPinA(void);
uint8_t ios_getEncoderPinB(void);
void ios_setLed(uint8_t index,uint8_t value);
void ios_setBocOut(uint8_t value);
void ios_setBocOut(uint8_t value);
