ernesto-g/modular-synth/FINISHED/LFOx3/Firmware/Main.ino/Waveforms.h

#define TABLE_SIZE  2048

extern const unsigned char SINETABLE[TABLE_SIZE];
extern const unsigned char TRIANGLETABLE[TABLE_SIZE];
extern const unsigned char EXPTABLE[TABLE_SIZE];
extern const unsigned char SAWTABLE[TABLE_SIZE];
extern const unsigned char RANDTABLE[TABLE_SIZE];


extern const unsigned int TABLE_POT_TO_FM[1024];
